FernandoB/strandberg/docs/5 way superswitch/Stewart-MacDonald_files/Steinberger_Gearless_Tuners.jpg

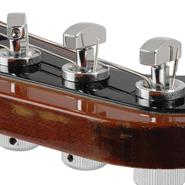
docs/5 way superswitch/Stewart-MacDonald_files/Steinberger_Gearless_Tuners.jpg
