FernandoB/strandberg/docs/#17 – Tosin Abasi _ Strandberg Guitarworks_files/IMG_47381-150x150.jpg

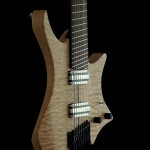
docs/#17 – Tosin Abasi _ Strandberg Guitarworks_files/IMG_47381-150x150.jpg
