FernandoB/strandberg/docs/#17 – Tosin Abasi _ Strandberg Guitarworks_files/Specs-17-150x150.jpg

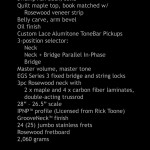
docs/#17 – Tosin Abasi _ Strandberg Guitarworks_files/Specs-17-150x150.jpg
