FernandoB/strandberg/docs/Asymmetric neck shapes – Käppi Guitars_files/Asymmetric-neck-shapes-1.png

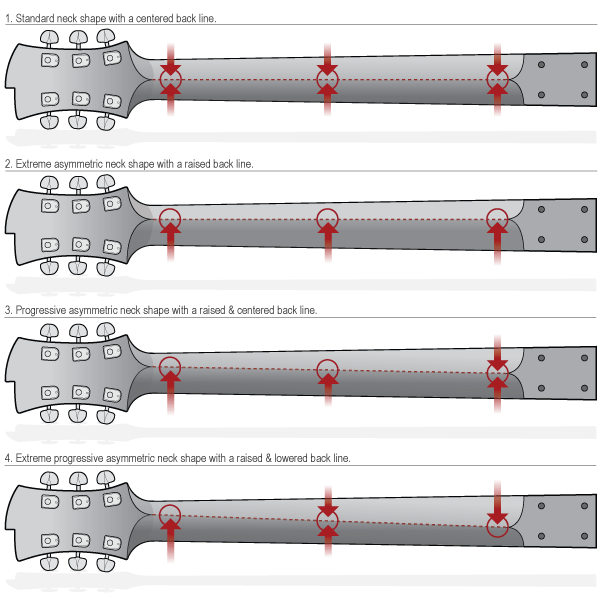
docs/Asymmetric neck shapes – Käppi Guitars_files/Asymmetric-neck-shapes-1.png
