FernandoB/strandberg/docs/boden metal white/bd7ct-17m-e-m-wp_1.png

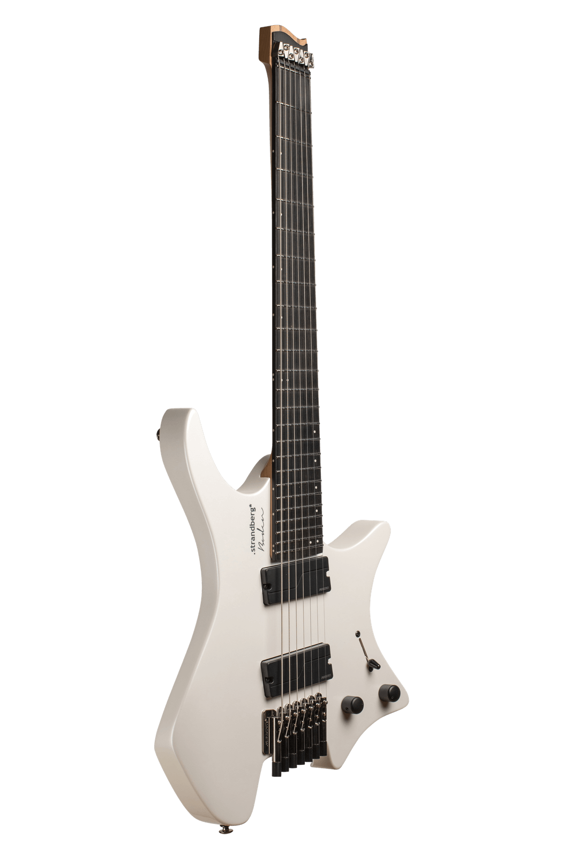
docs/boden metal white/bd7ct-17m-e-m-wp_1.png
