FernandoB/strandberg/docs/body/IMG_1061-465x620.jpg

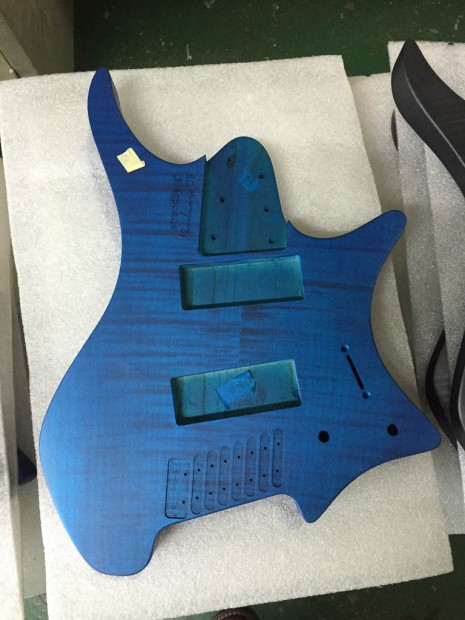
docs/body/IMG_1061-465x620.jpg
