FernandoB/strandberg/docs/body/IMG_6017.jpg

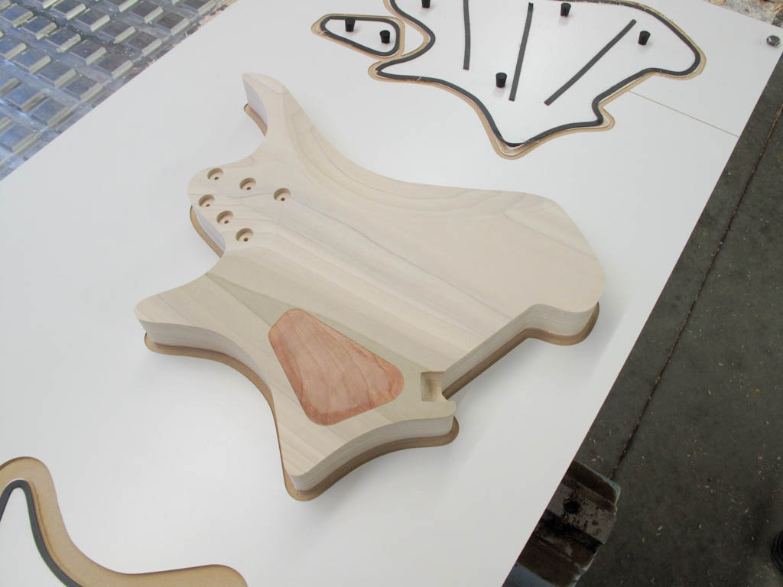
docs/body/IMG_6017.jpg
