FernandoB/strandberg/docs/body/IMG_6269.jpg

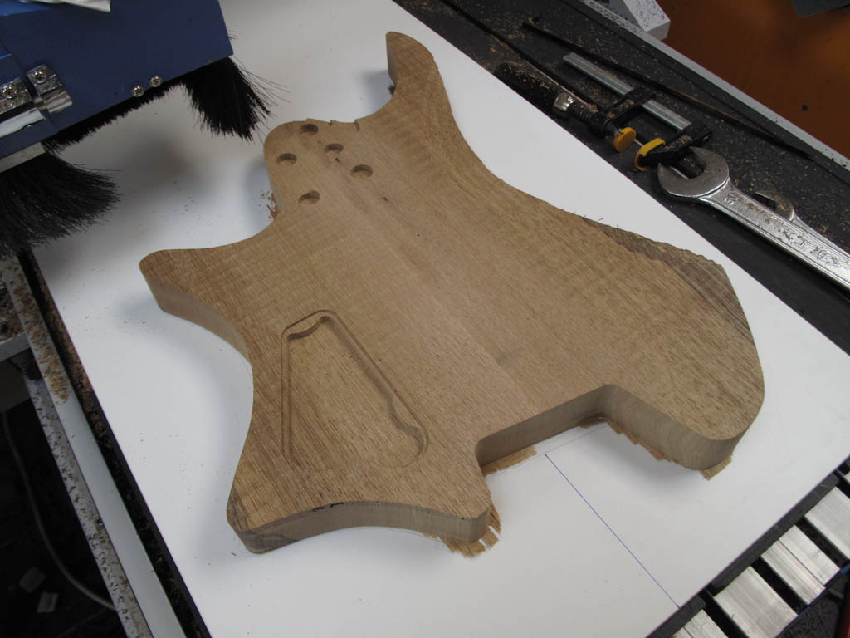
docs/body/IMG_6269.jpg
