FernandoB/strandberg/docs/fotos/5696bf7990480f4bdb856ef551d9e4b1.jpg

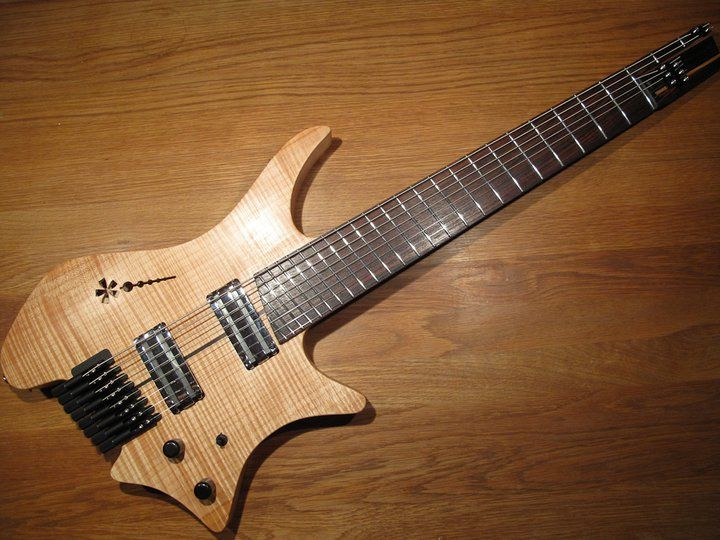
docs/fotos/5696bf7990480f4bdb856ef551d9e4b1.jpg
