FernandoB/strandberg/docs/mango/Patent Pending – The EndurNeck _ Strandberg Guitarworks_files/7s-twist.jpg

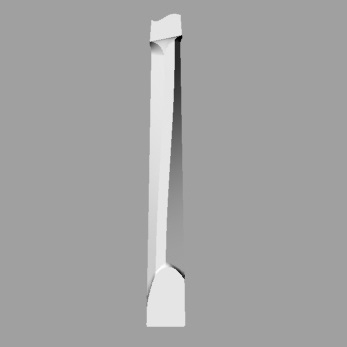
docs/mango/Patent Pending – The EndurNeck _ Strandberg Guitarworks_files/7s-twist.jpg
