FernandoB/strandberg/docs/NorthStar 8-string headless - Page 2 - In Progress and Finished Work - ProjectGuitar.com_files/IMG_1043_zpse3bc9081.jpg

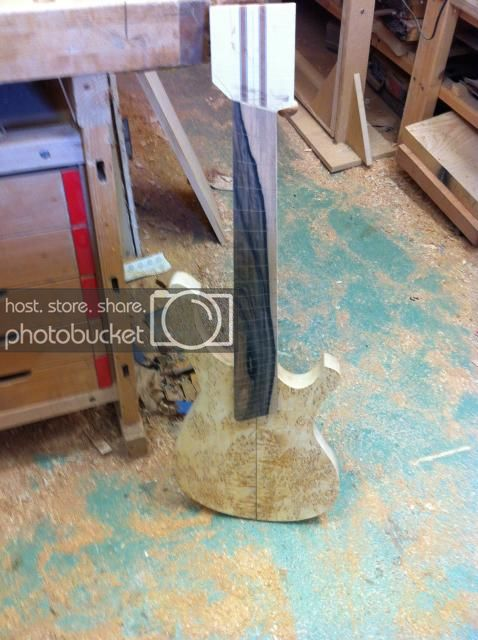
docs/NorthStar 8-string headless - Page 2 - In Progress and Finished Work - ProjectGuitar.com_files/IMG_1043_zpse3bc9081.jpg
