FernandoB/strandberg/docs/NorthStar 8-string headless - Page 2 - In Progress and Finished Work - ProjectGuitar.com_files/IMG_1084_zps51eaacd9.jpg

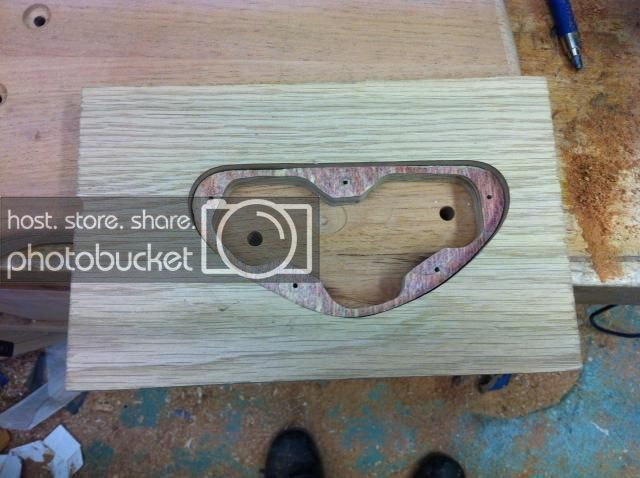
docs/NorthStar 8-string headless - Page 2 - In Progress and Finished Work - ProjectGuitar.com_files/IMG_1084_zps51eaacd9.jpg
