FernandoB/strandberg/docs/NorthStar 8-string headless - Page 2 - In Progress and Finished Work - ProjectGuitar.com_files/P4180146.jpg

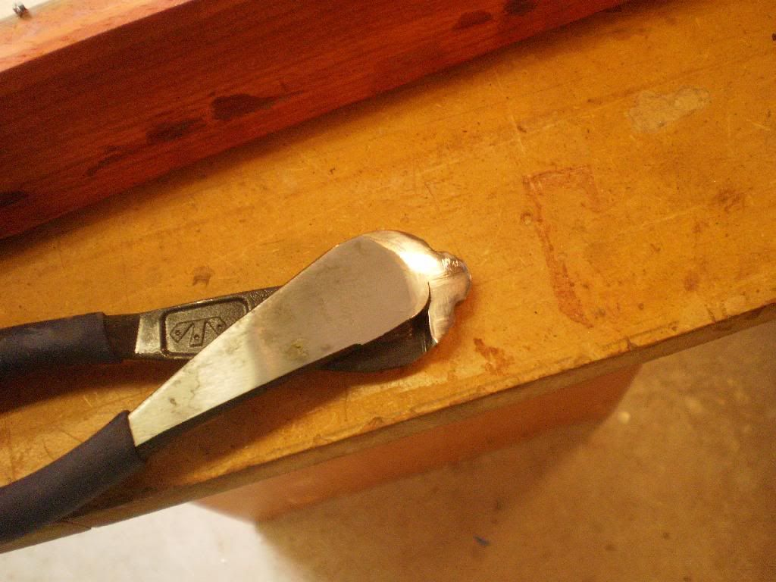
docs/NorthStar 8-string headless - Page 2 - In Progress and Finished Work - ProjectGuitar.com_files/P4180146.jpg
