FernandoB/strandberg/docs/specs/Boden Classic 7 Ghost White _ .strandberg_ Guitars_files/67343479_150905999349722_2680000513504285173_n.jpg

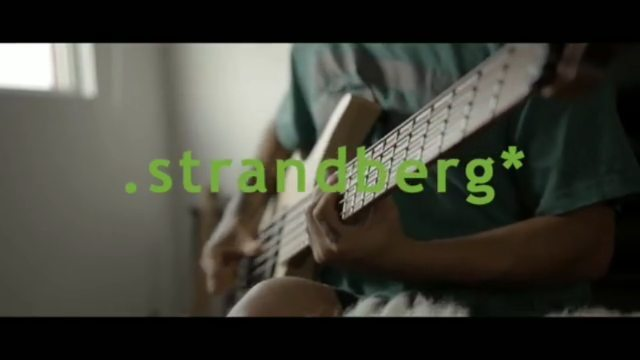
docs/specs/Boden Classic 7 Ghost White _ .strandberg_ Guitars_files/67343479_150905999349722_2680000513504285173_n.jpg
