FernandoB/strandberg/docs/specs/Boden Classic 7 Ghost White _ .strandberg_ Guitars_files/67426803_511736299582143_8697421153145143601_n.jpg

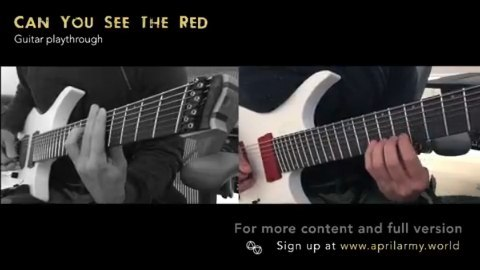
docs/specs/Boden Classic 7 Ghost White _ .strandberg_ Guitars_files/67426803_511736299582143_8697421153145143601_n.jpg
