FernandoB/strandberg/docs/specs/Boden Classic 7 Ghost White _ .strandberg_ Guitars_files/67452516_102354637756186_6294496770134847847_n.jpg

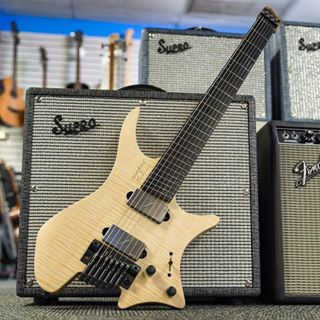
docs/specs/Boden Classic 7 Ghost White _ .strandberg_ Guitars_files/67452516_102354637756186_6294496770134847847_n.jpg
