FernandoB/strandberg/docs/specs/Boden Classic 7 Ghost White _ .strandberg_ Guitars_files/67589641_469000926987436_5073157512534394637_n.jpg

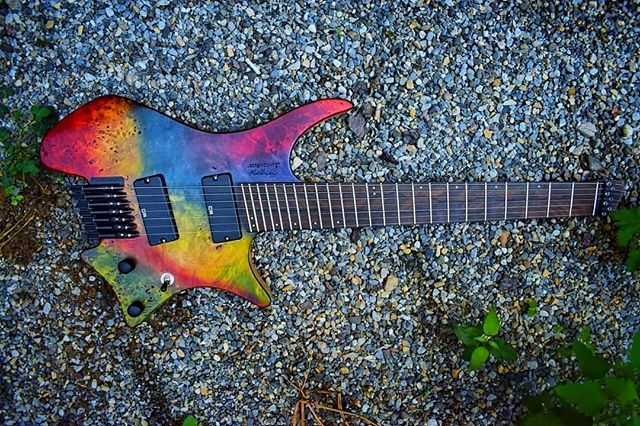
docs/specs/Boden Classic 7 Ghost White _ .strandberg_ Guitars_files/67589641_469000926987436_5073157512534394637_n.jpg
