FernandoB/strandberg/docs/specs/Boden Classic 7 Ghost White _ .strandberg_ Guitars_files/67694899_190797451917939_3582394010340054068_n.jpg

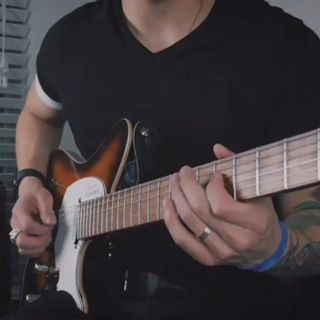
docs/specs/Boden Classic 7 Ghost White _ .strandberg_ Guitars_files/67694899_190797451917939_3582394010340054068_n.jpg
