FernandoB/strandberg/docs/specs/Boden Classic 7 Ghost White _ .strandberg_ Guitars_files/68956459_2375854755962711_6913870519651780243_n.jpg

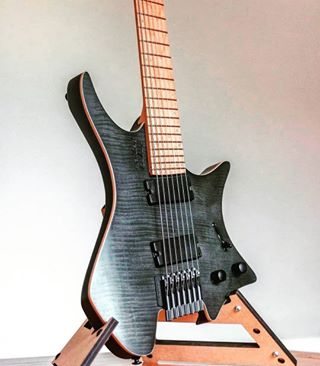
docs/specs/Boden Classic 7 Ghost White _ .strandberg_ Guitars_files/68956459_2375854755962711_6913870519651780243_n.jpg
