FernandoB/strandberg/docs/specs/Boden Classic 7 Ghost White _ .strandberg_ Guitars_files/68979052_158855945174218_2727487326449297141_n.jpg

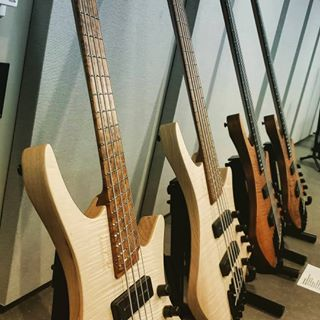
docs/specs/Boden Classic 7 Ghost White _ .strandberg_ Guitars_files/68979052_158855945174218_2727487326449297141_n.jpg
