FernandoB/strandberg/docs/specs/Boden Classic 7 Ghost White _ .strandberg_ Guitars_files/69485622_2290564877940070_366146129192254861_n.jpg

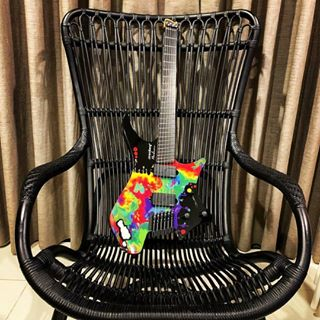
docs/specs/Boden Classic 7 Ghost White _ .strandberg_ Guitars_files/69485622_2290564877940070_366146129192254861_n.jpg
