FernandoB/strandberg/docs/specs/Boden Classic 7 Ghost White _ .strandberg_ Guitars_files/69579608_494088754658758_1485637827757459320_n.jpg

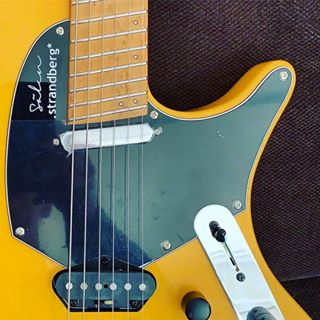
docs/specs/Boden Classic 7 Ghost White _ .strandberg_ Guitars_files/69579608_494088754658758_1485637827757459320_n.jpg
