FernandoB/strandberg/docs/specs/Boden Classic 7 Ghost White _ .strandberg_ Guitars_files/69621913_944535012569313_5548777814130400954_n.jpg

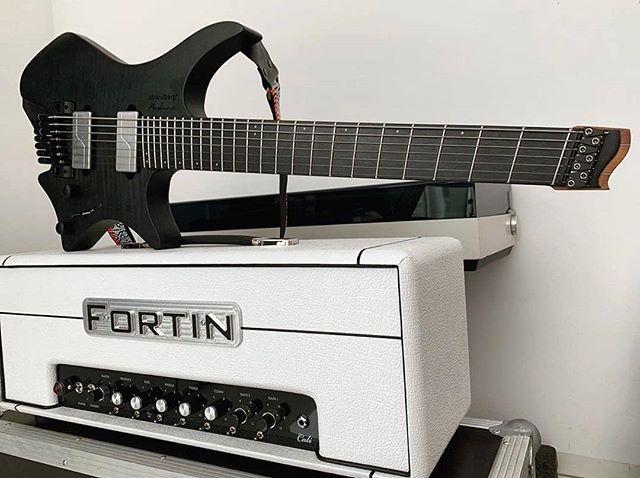
docs/specs/Boden Classic 7 Ghost White _ .strandberg_ Guitars_files/69621913_944535012569313_5548777814130400954_n.jpg
