FernandoB/strandberg/docs/specs/Boden Classic 7 Ghost White _ .strandberg_ Guitars_files/bd7ct-17o-m-f-bk_a-606x909.webp

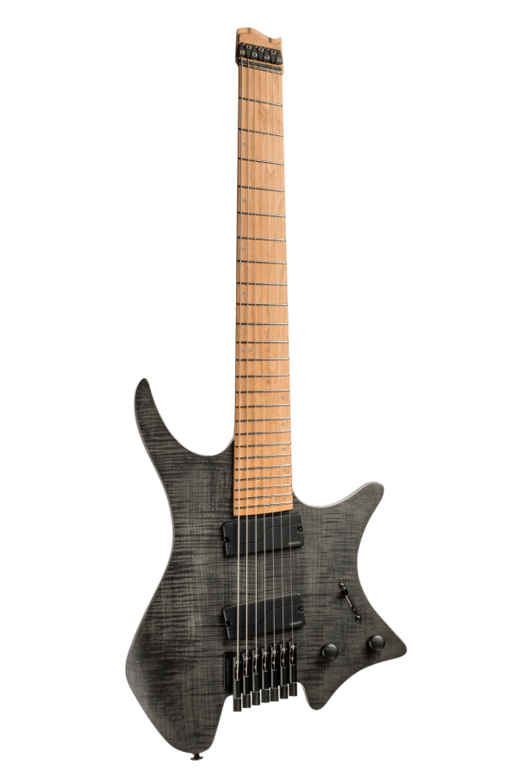
docs/specs/Boden Classic 7 Ghost White _ .strandberg_ Guitars_files/bd7ct-17o-m-f-bk_a-606x909.webp
