FernandoB/strandberg/docs/specs/Boden Classic 7 Ghost White _ .strandberg_ Guitars_files/bd7ct-18c-m-a-gw_4-160x240.png

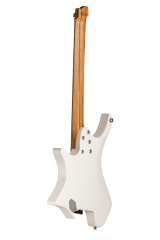
docs/specs/Boden Classic 7 Ghost White _ .strandberg_ Guitars_files/bd7ct-18c-m-a-gw_4-160x240.png
