FernandoB/strandberg/docs/specs/Boden Classic 7 Ghost White _ .strandberg_ Guitars_files/bkg-boden-classic.webp

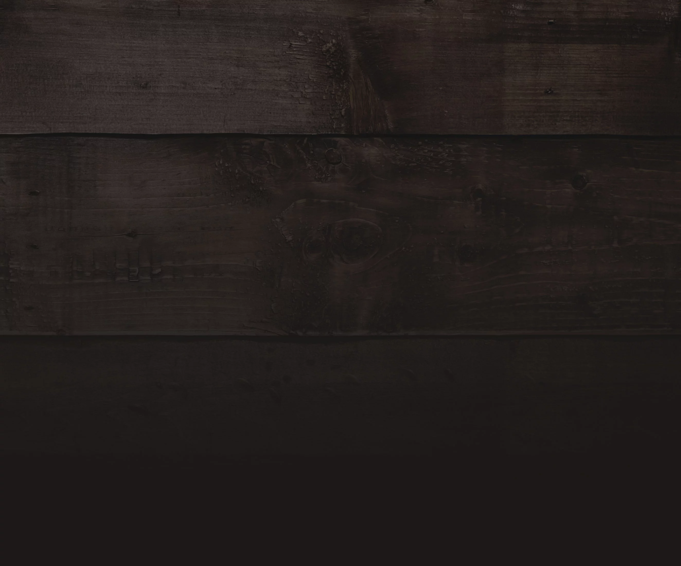
docs/specs/Boden Classic 7 Ghost White _ .strandberg_ Guitars_files/bkg-boden-classic.webp
