FernandoB/strandberg/docs/specs/Boden Classic 7 Ghost White _ .strandberg_ Guitars_files/boden_classic_beauty_shot_1.webp

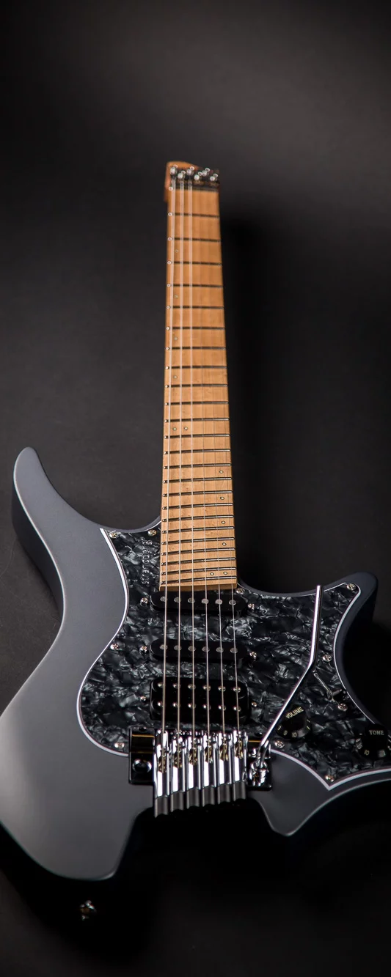
docs/specs/Boden Classic 7 Ghost White _ .strandberg_ Guitars_files/boden_classic_beauty_shot_1.webp
