FernandoB/strandberg/docs/specs/Boden Classic 7 Ghost White _ .strandberg_ Guitars_files/boden_machacek_beauty_shot_7-720x664.webp

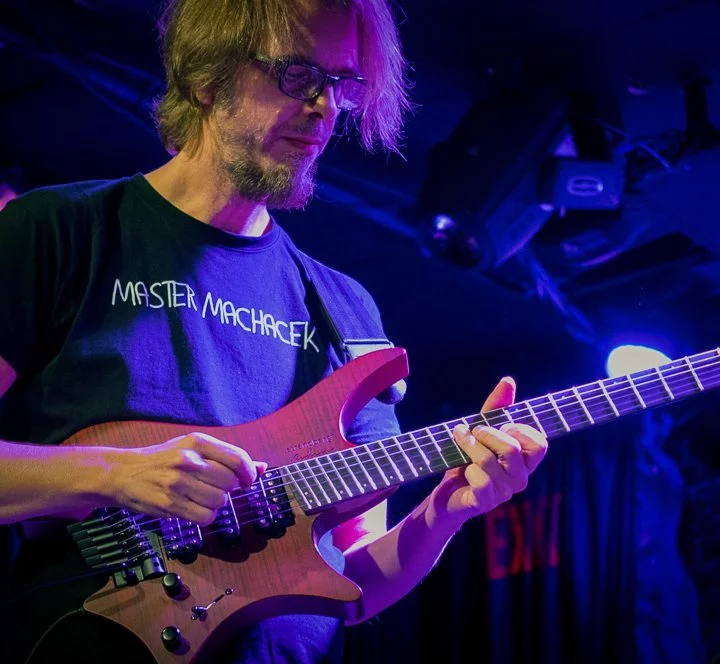
docs/specs/Boden Classic 7 Ghost White _ .strandberg_ Guitars_files/boden_machacek_beauty_shot_7-720x664.webp
