FernandoB/strandberg/docs/specs/Boden Classic 7 Ghost White _ .strandberg_ Guitars_files/headless_design_bullet_round-150x150.webp

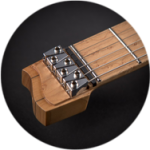
docs/specs/Boden Classic 7 Ghost White _ .strandberg_ Guitars_files/headless_design_bullet_round-150x150.webp
