FernandoB/strandberg/docs/specs/Boden Classic 7 Ghost White _ .strandberg_ Guitars_files/img_8952-e1481700775124-720x720.webp

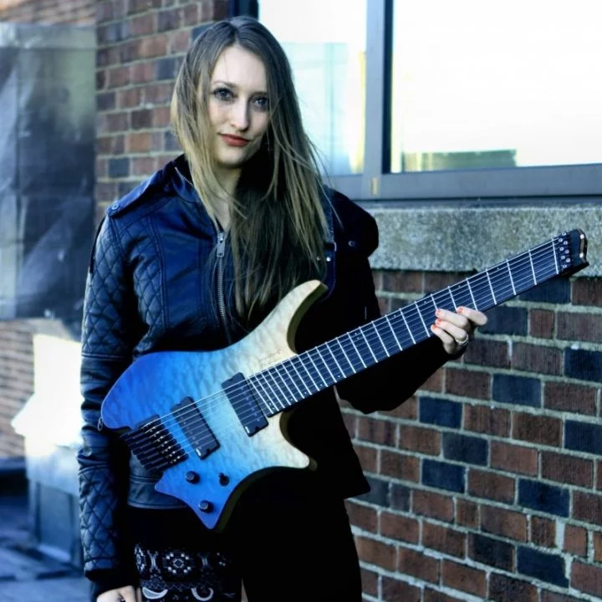
docs/specs/Boden Classic 7 Ghost White _ .strandberg_ Guitars_files/img_8952-e1481700775124-720x720.webp
