FernandoB/strandberg/docs/specs/Boden Classic 7 Ghost White _ .strandberg_ Guitars_files/mike_keneally_landscape-720x720.webp

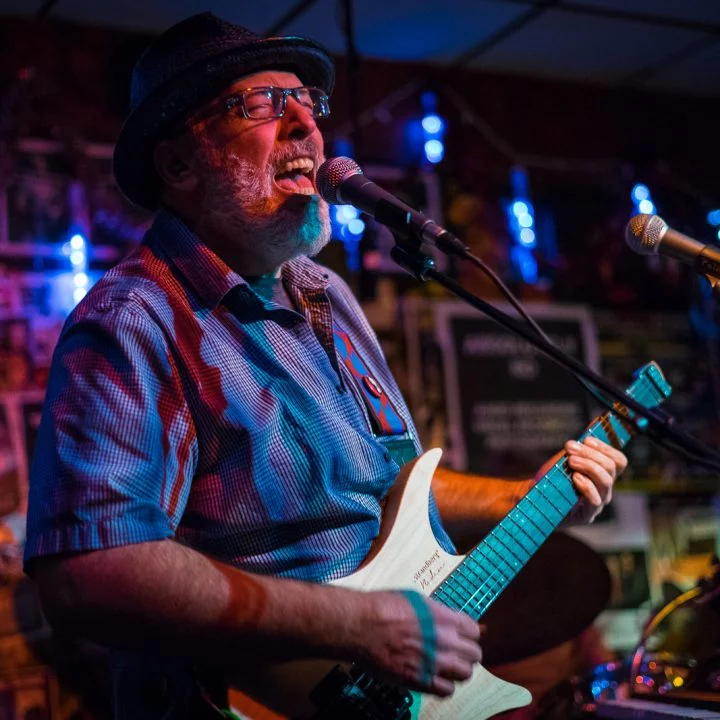
docs/specs/Boden Classic 7 Ghost White _ .strandberg_ Guitars_files/mike_keneally_landscape-720x720.webp
