FernandoB/strandberg/docs/specs/Boden Metal 7 White Pearl _ .strandberg_ Guitars_files/bd7ct-17m-e-m-wp_c-160x240.webp

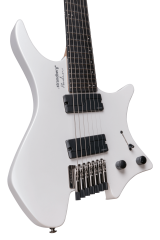
docs/specs/Boden Metal 7 White Pearl _ .strandberg_ Guitars_files/bd7ct-17m-e-m-wp_c-160x240.webp
