FernandoB/strandberg/docs/specs/Boden Metal 7 White Pearl _ .strandberg_ Guitars_files/bkg-metal.webp

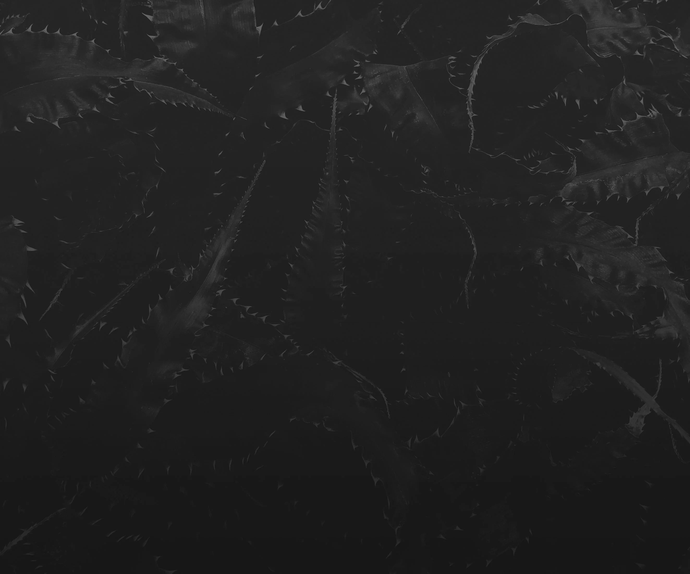
docs/specs/Boden Metal 7 White Pearl _ .strandberg_ Guitars_files/bkg-metal.webp
