FernandoB/strandberg/docs/specs/Boden Metal 7 White Pearl _ .strandberg_ Guitars_files/boden_metal_beauty_shot_2.webp

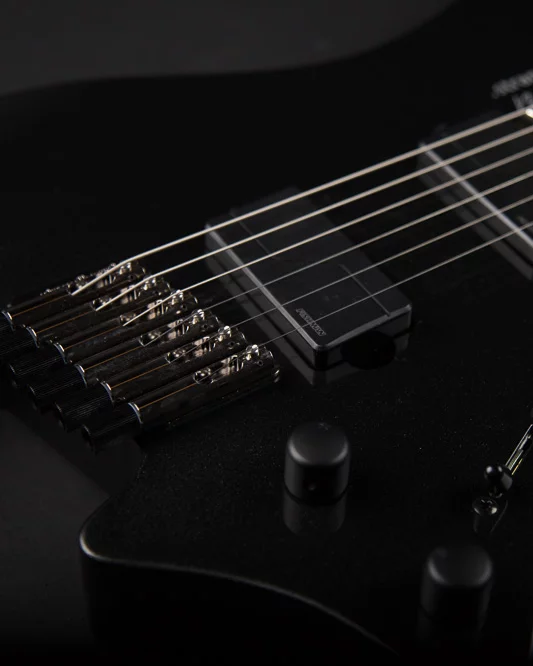
docs/specs/Boden Metal 7 White Pearl _ .strandberg_ Guitars_files/boden_metal_beauty_shot_2.webp
