FernandoB/strandberg/docs/specs/Boden Standard 7 Maple Flame Blue _ .strandberg_ Guitars_files/bd7ct-18s-m-fv-bl_1-160x240.webp

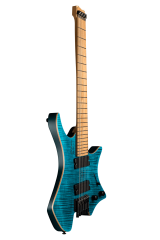
docs/specs/Boden Standard 7 Maple Flame Blue _ .strandberg_ Guitars_files/bd7ct-18s-m-fv-bl_1-160x240.webp
