FernandoB/strandberg/docs/specs/Boden Standard 7 Maple Flame Blue _ .strandberg_ Guitars_files/bd7tct-17o-m-f-rd_a-606x909.webp

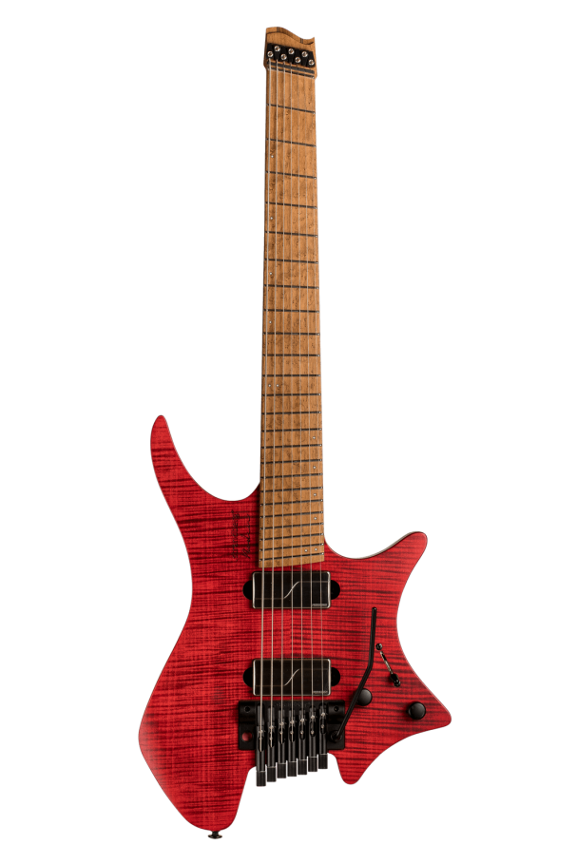
docs/specs/Boden Standard 7 Maple Flame Blue _ .strandberg_ Guitars_files/bd7tct-17o-m-f-rd_a-606x909.webp
