FernandoB/strandberg/docs/specs/Boden Standard 7 Maple Flame Blue _ .strandberg_ Guitars_files/bkg-standard.jpg

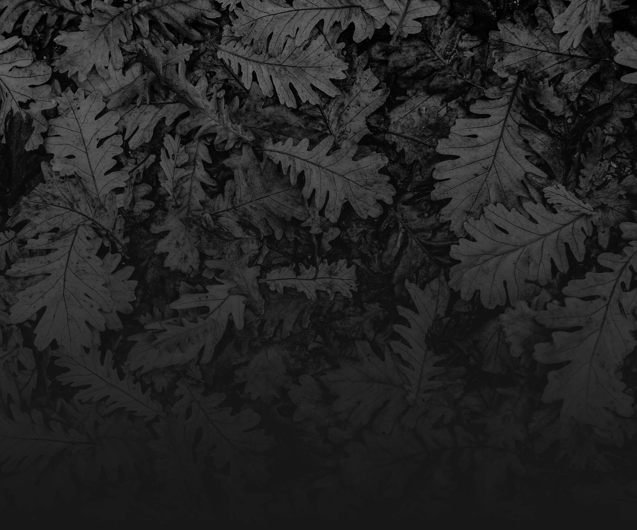
docs/specs/Boden Standard 7 Maple Flame Blue _ .strandberg_ Guitars_files/bkg-standard.jpg
