FernandoB/strandberg/docs/specs/Boden Standard 7 Maple Flame Blue _ .strandberg_ Guitars_files/boden_standard_beauty_shot_1.webp

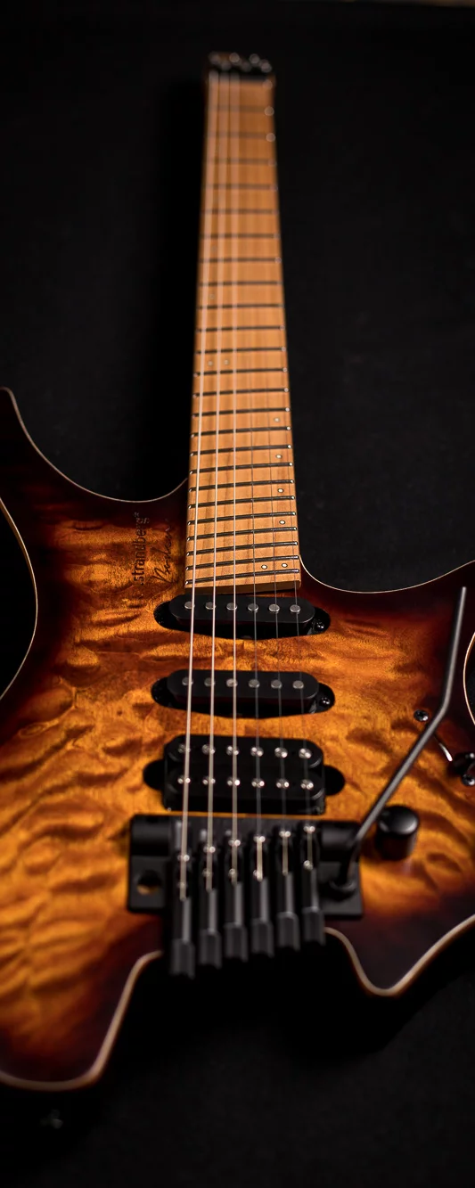
docs/specs/Boden Standard 7 Maple Flame Blue _ .strandberg_ Guitars_files/boden_standard_beauty_shot_1.webp
