FernandoB/strandberg/docs/wiring/#61 Wiring _ Strandberg Guitarworks_files/61-Schematic-300x217.png

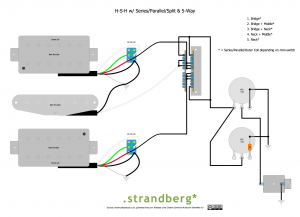
docs/wiring/#61 Wiring _ Strandberg Guitarworks_files/61-Schematic-300x217.png
