FernandoB/strandberg/docs/wiring/#65 Wiring _ Strandberg Guitarworks_files/65-Schematic-300x217.png

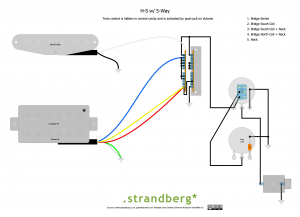
docs/wiring/#65 Wiring _ Strandberg Guitarworks_files/65-Schematic-300x217.png
