FernandoB/strandberg/photos/20210119_215234.jpg

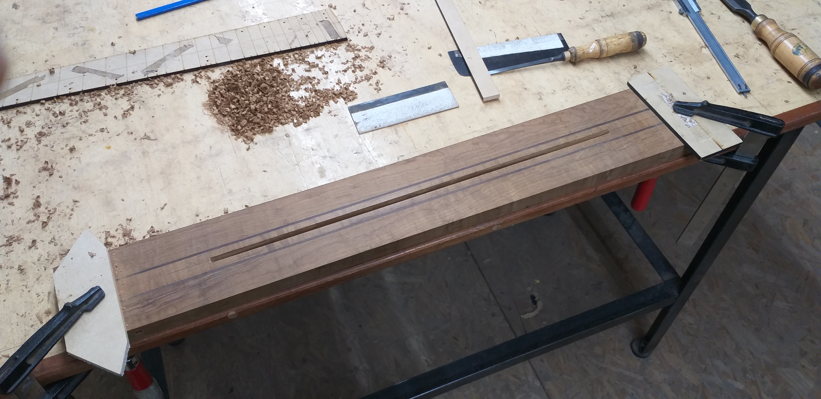
photos/20210119_215234.jpg
