FernandoB/strandberg/photos/20210209_213849.jpg

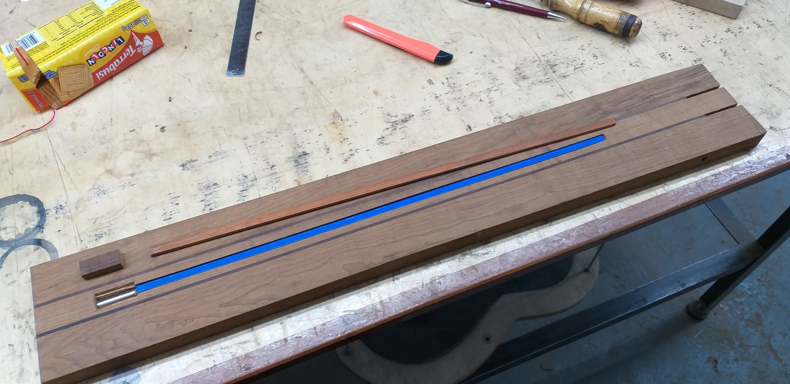
photos/20210209_213849.jpg
