FernandoB/strandberg/photos/20210223_215921.jpg

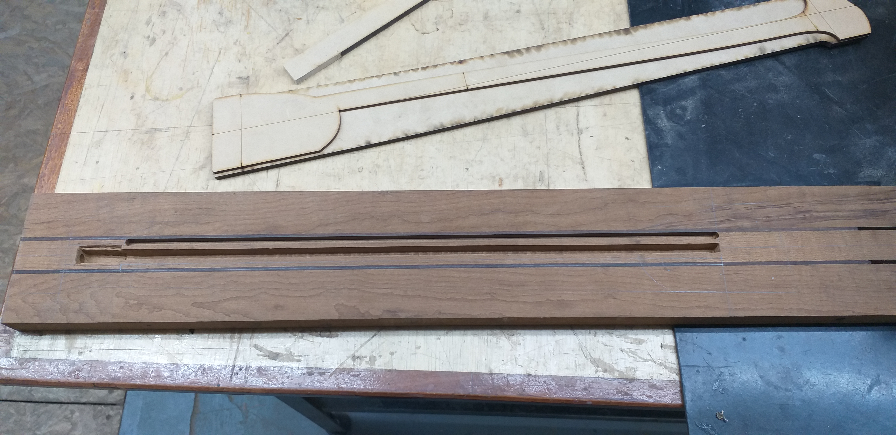
photos/20210223_215921.jpg
