FernandoB/strandberg/photos/20210330_215819.jpg

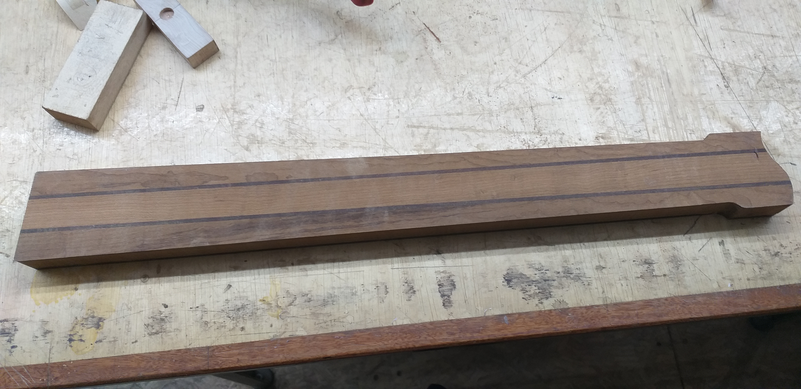
photos/20210330_215819.jpg
