FernandoB/strandberg/photos/20210406_194518.jpg

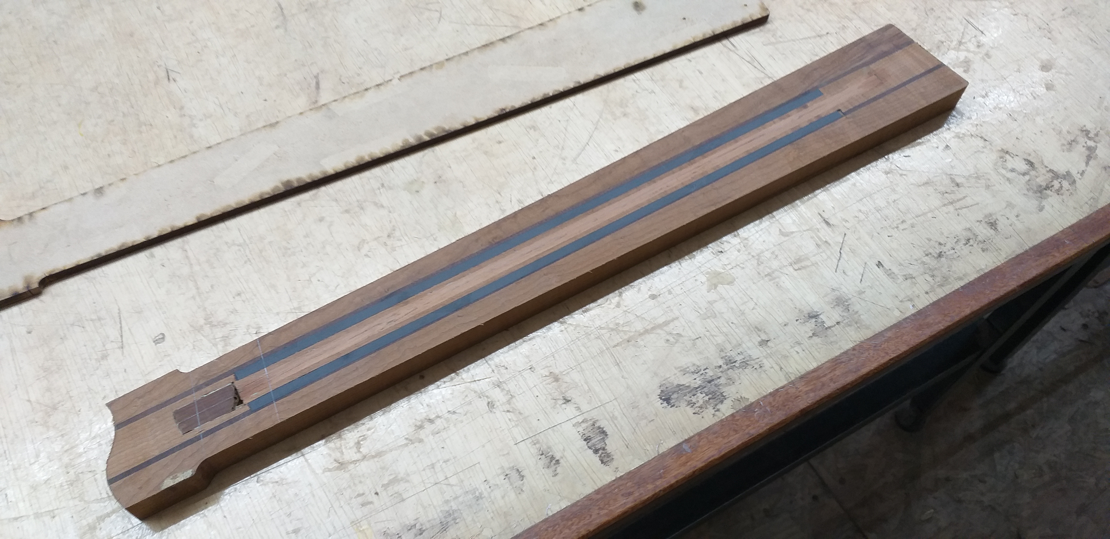
photos/20210406_194518.jpg
