FernandoB/strandberg/photos/20210427_192807.jpg

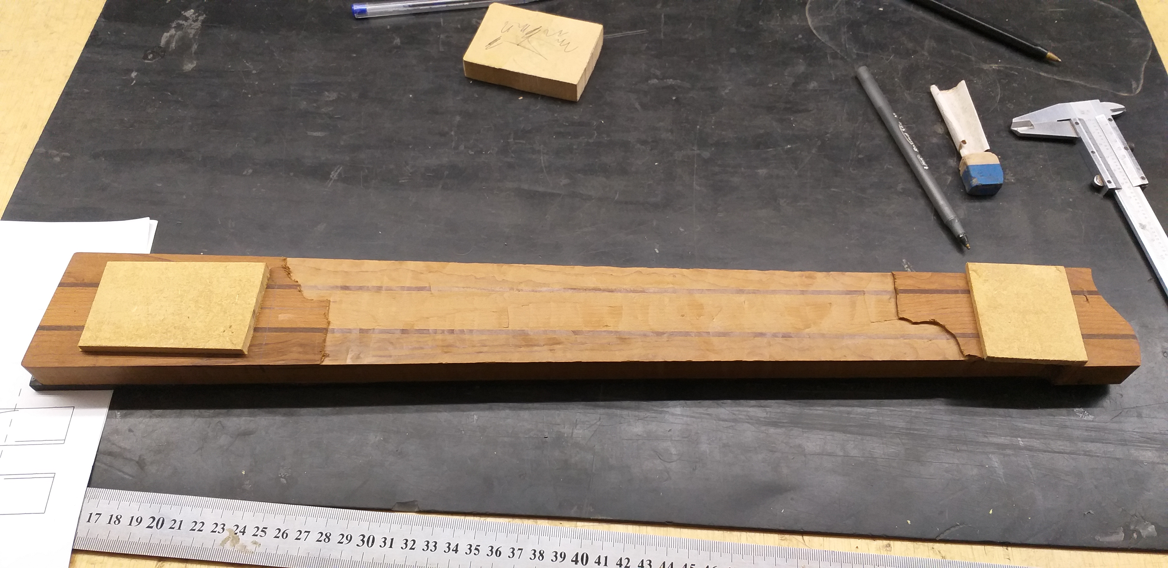
photos/20210427_192807.jpg
