FernandoB/strandberg/photos/20210713_215407.jpg

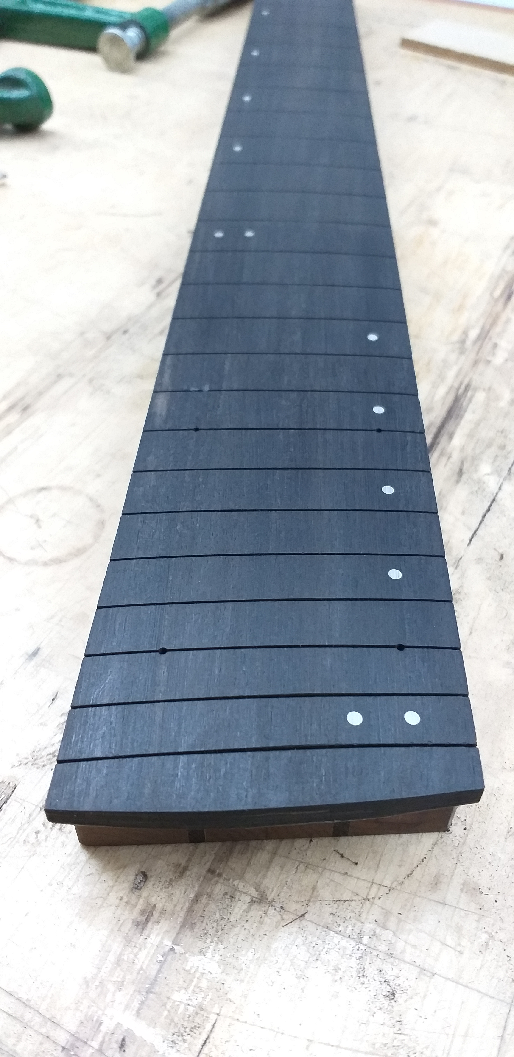
photos/20210713_215407.jpg
