FernandoB/strandberg/photos/20211012_215354.jpg

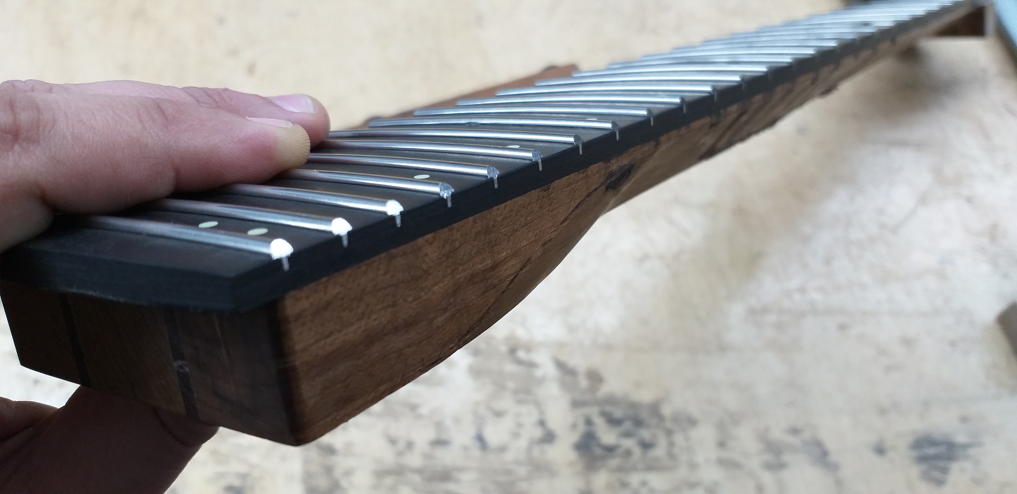
photos/20211012_215354.jpg
