FernandoB/strandberg/photos/20220315_215535.jpg

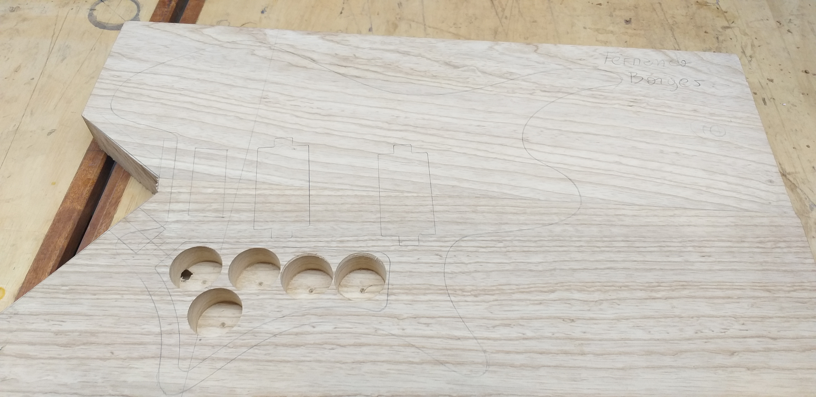
photos/20220315_215535.jpg
