FernandoB/strandberg/photos/20220329_215044.jpg

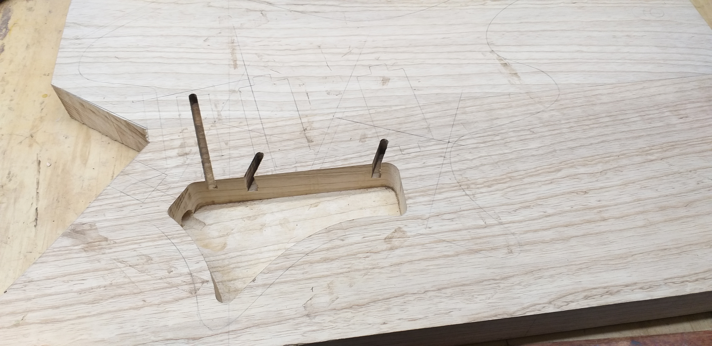
photos/20220329_215044.jpg
