FernandoB/strandberg/photos/20220419_215206.jpg

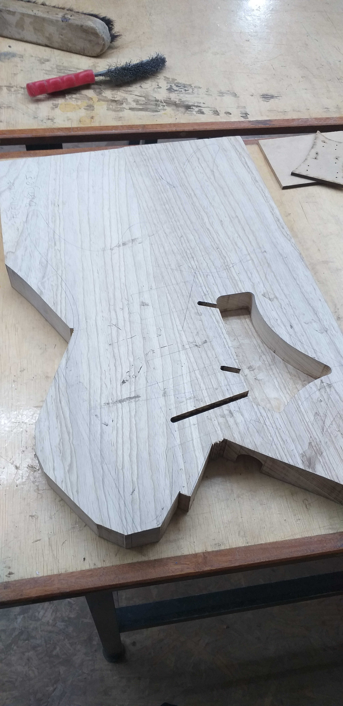
photos/20220419_215206.jpg
