FernandoB/strandberg/photos/20220614_215217.jpg

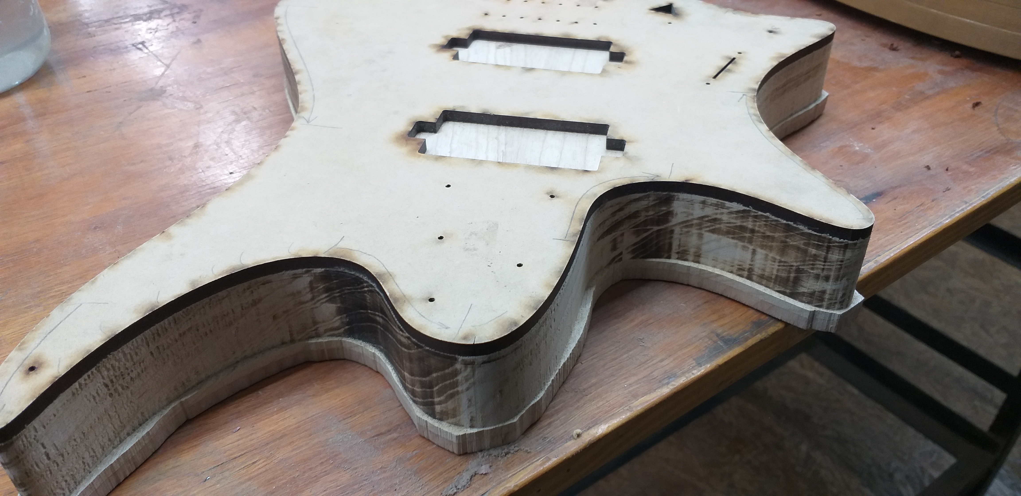
photos/20220614_215217.jpg
