FernandoB/strandberg/photos/20221004_215103.jpg

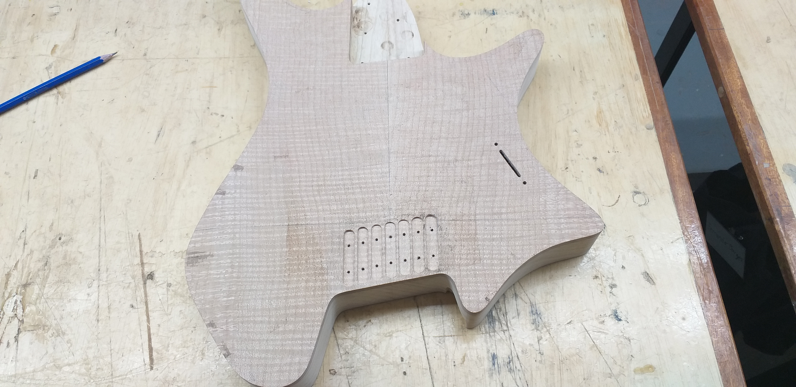
photos/20221004_215103.jpg
