FernandoB/strandberg/photos/20221018_213631.jpg

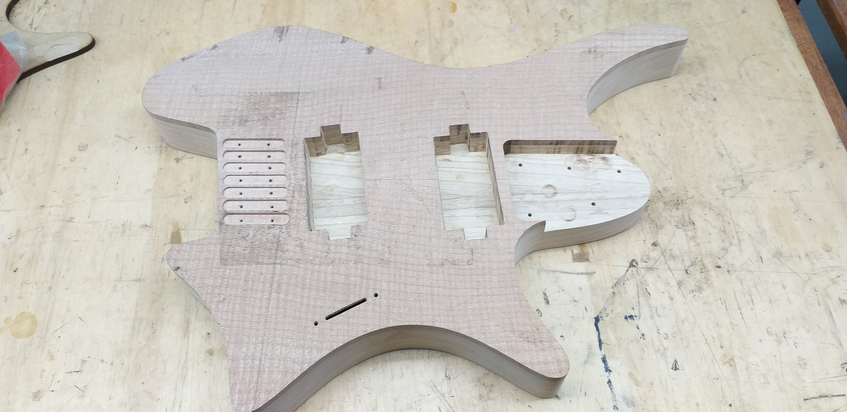
photos/20221018_213631.jpg
