FernandoB/strandberg/photos/20221018_215050.jpg

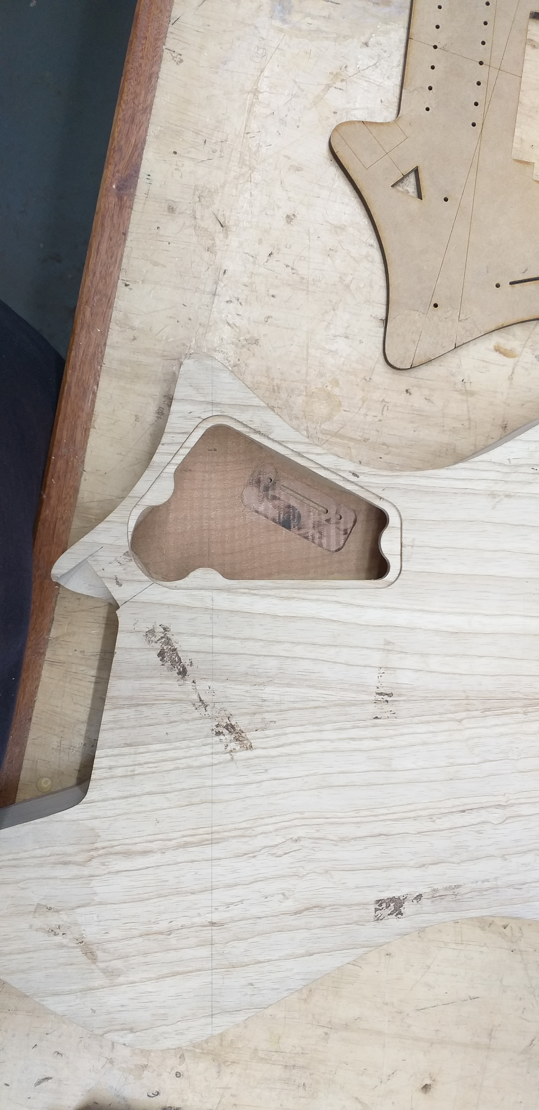
photos/20221018_215050.jpg
