FernandoB/strandberg/photos/20221018_215109.jpg

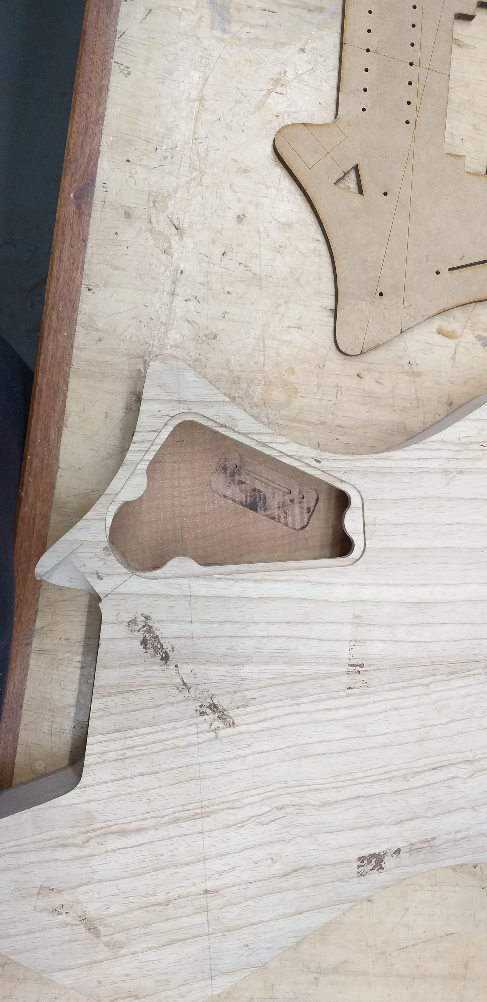
photos/20221018_215109.jpg
