FernandoB/strandberg/photos/20221108_215148.jpg

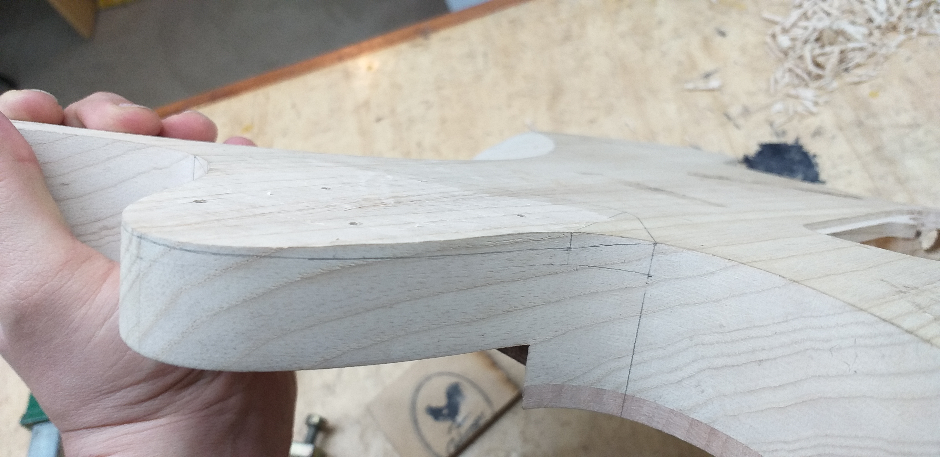
photos/20221108_215148.jpg
