FernandoB/strandberg/photos/20221115_215245.jpg

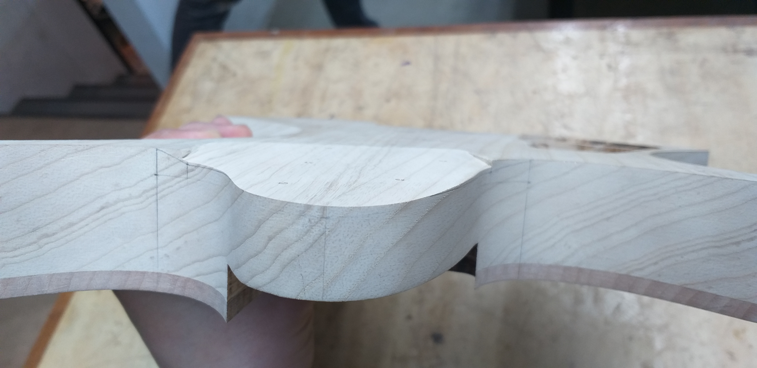
photos/20221115_215245.jpg
