FernandoB/strandberg/photos/20221122_213335.jpg

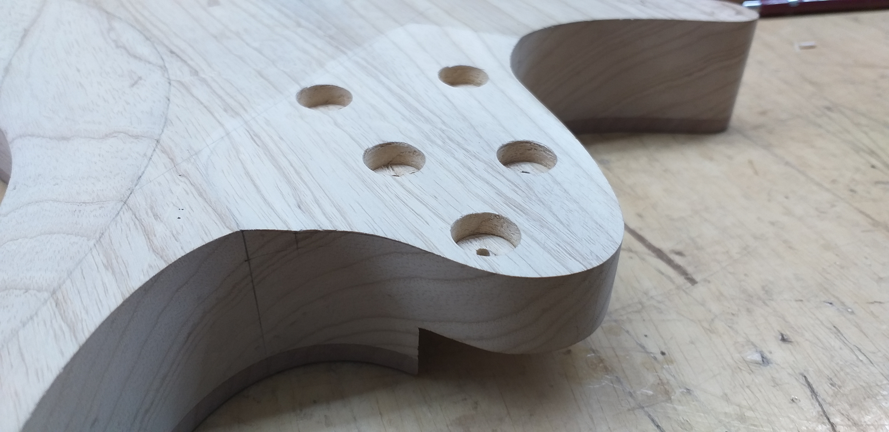
photos/20221122_213335.jpg
