FernandoB/strandberg/photos/20221222_201924.jpg

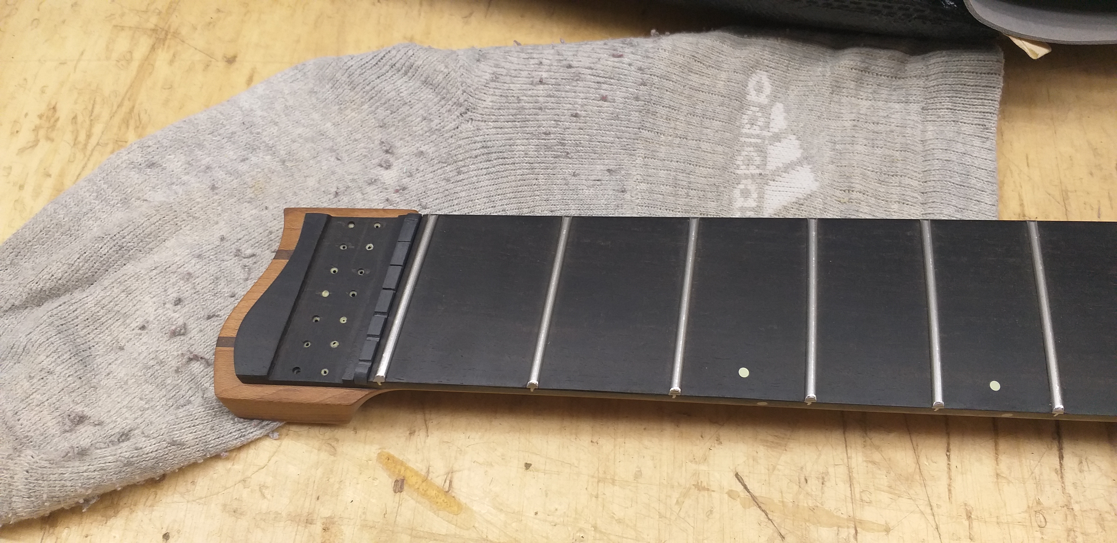
photos/20221222_201924.jpg
