FernandoB/strandberg/photos/20230228_214408.jpg

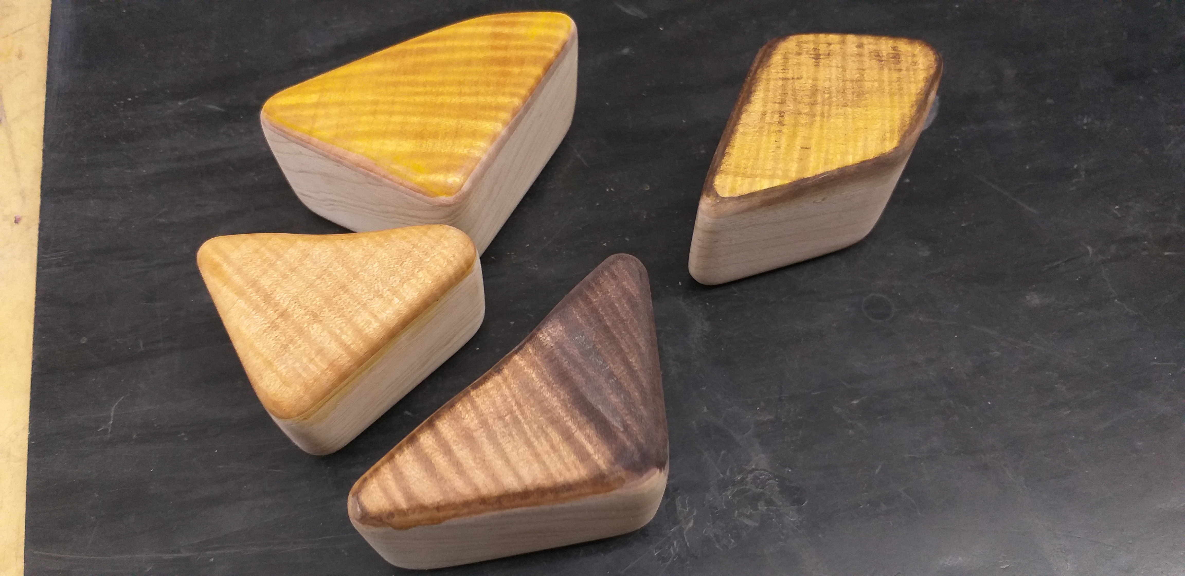
photos/20230228_214408.jpg
