FernandoB/strandberg/photos/20230411_212509.jpg

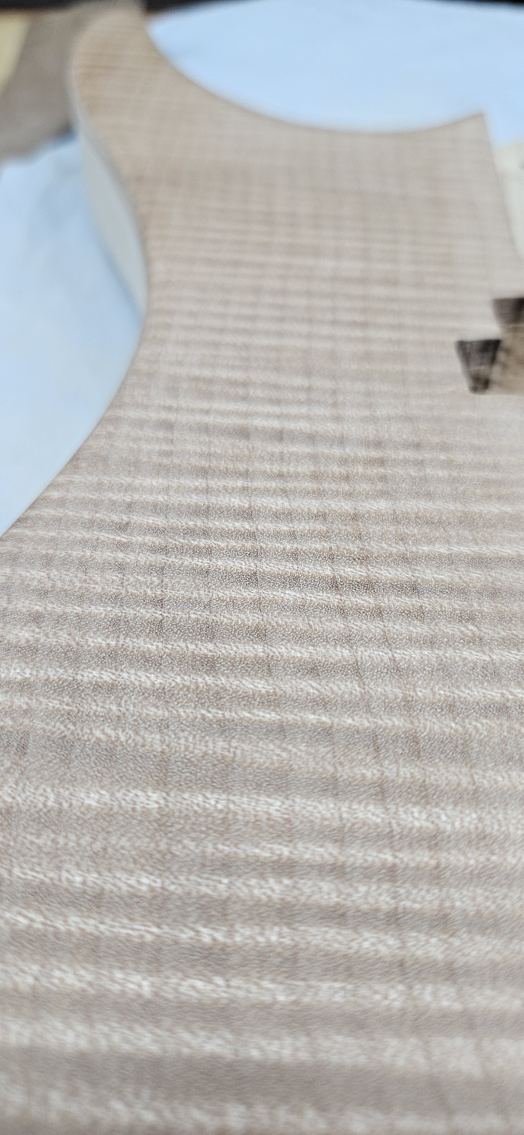
photos/20230411_212509.jpg
