FernandoB/strandberg/photos/20230411_212559.jpg

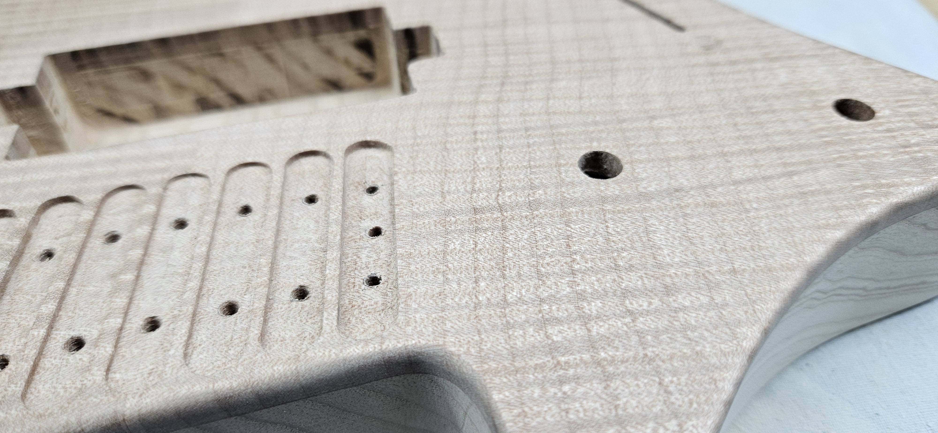
photos/20230411_212559.jpg
