FernandoB/strandberg/photos/20230530_205302.jpg

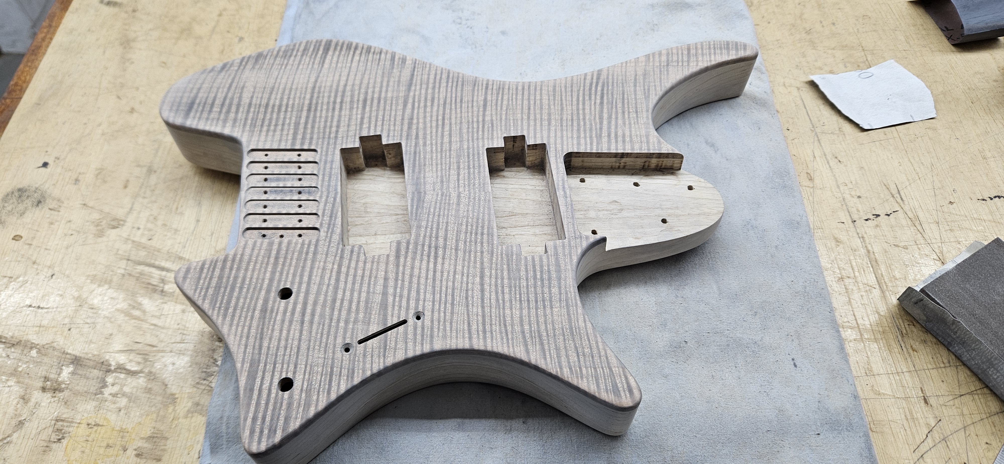
photos/20230530_205302.jpg
