FernandoB/strandberg/photos/20230530_215438.jpg

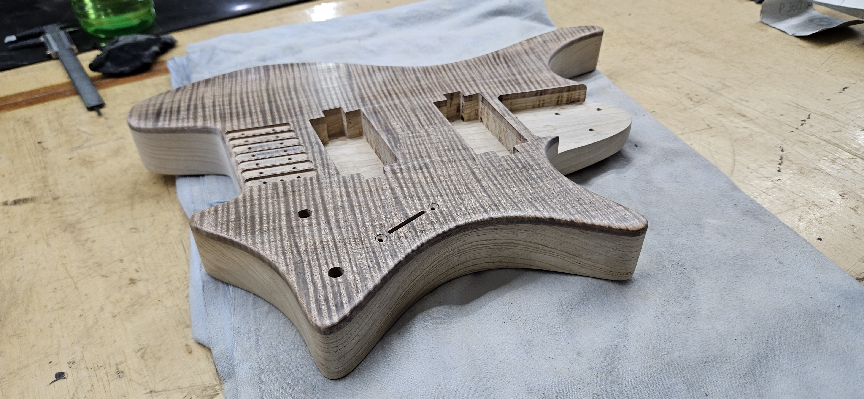
photos/20230530_215438.jpg
