FernandoB/strandberg/photos/20230711_215309.jpg

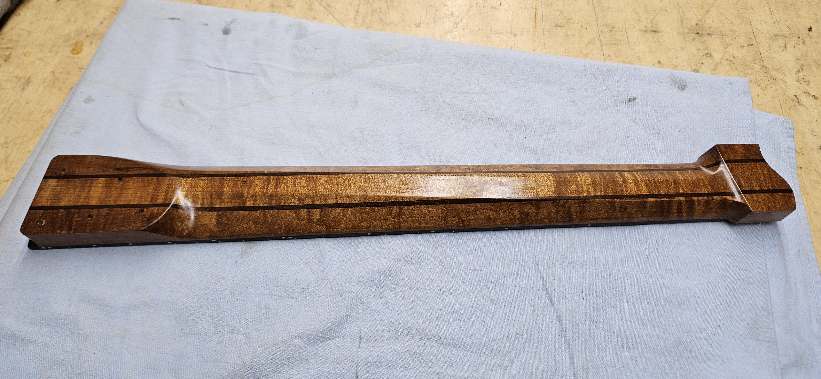
photos/20230711_215309.jpg
