FernandoB/strandberg/photos/20230808_203318.jpg

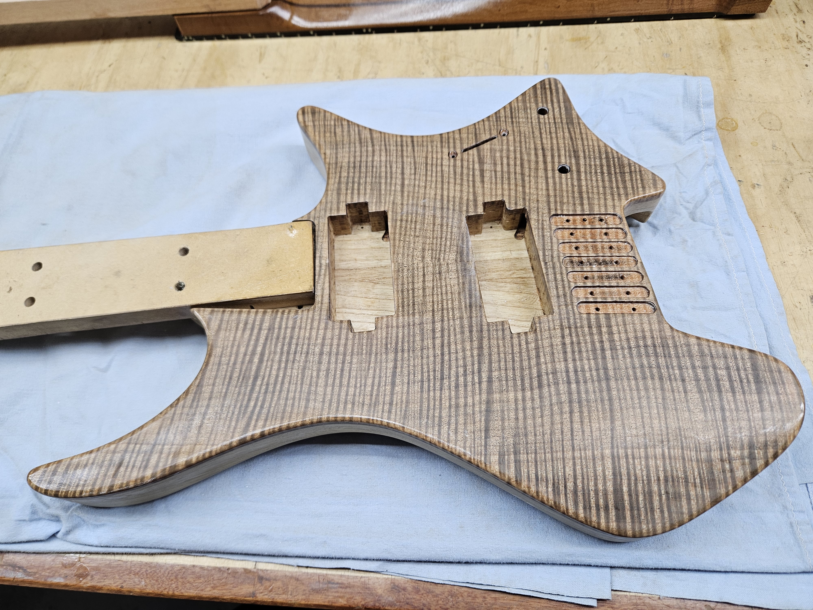
photos/20230808_203318.jpg
