FernandoB/strandberg/photos/20231010_213619.jpg

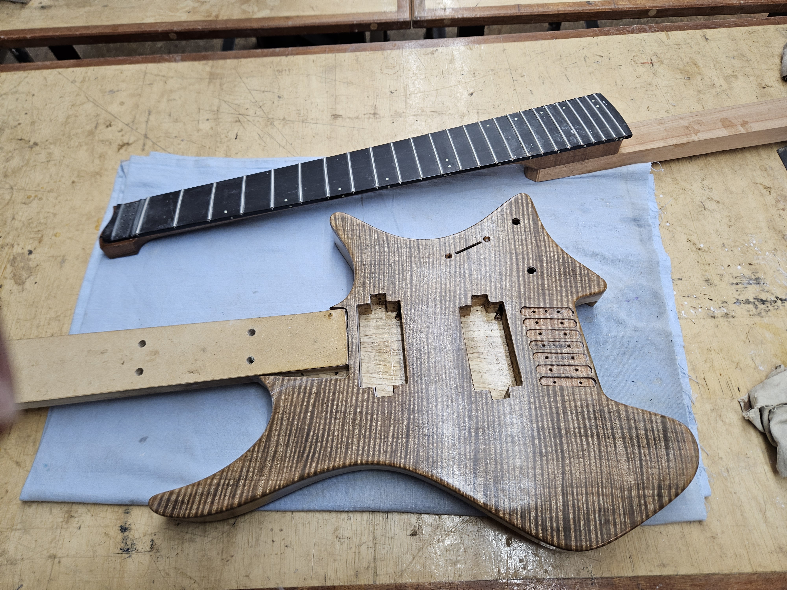
photos/20231010_213619.jpg
