FernandoB/strandberg/photos/20240723_220008.jpg

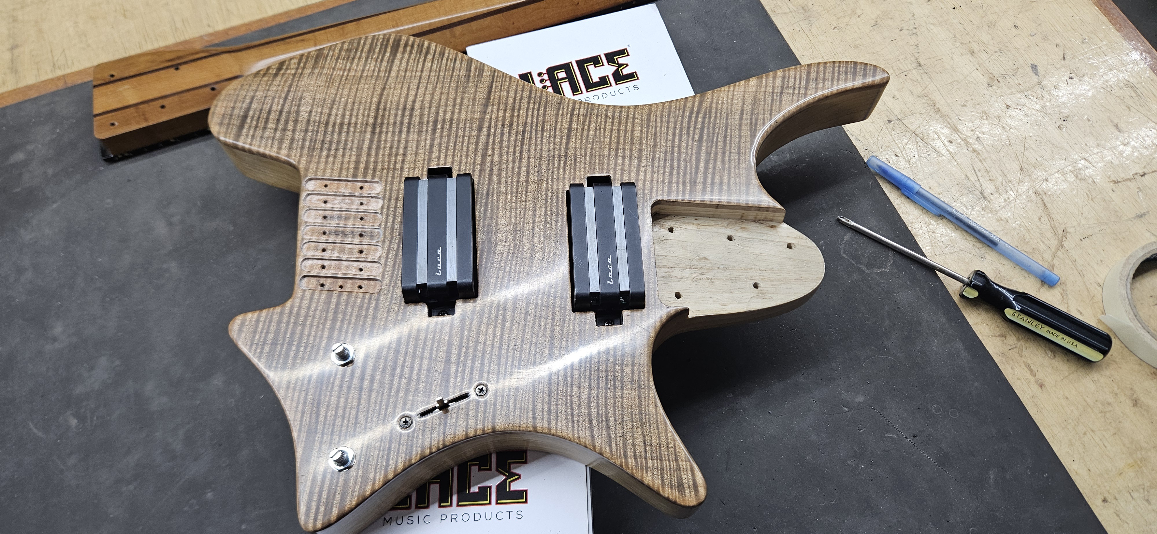
photos/20240723_220008.jpg
