FernandoB/strandberg/photos/20240730_210756.jpg

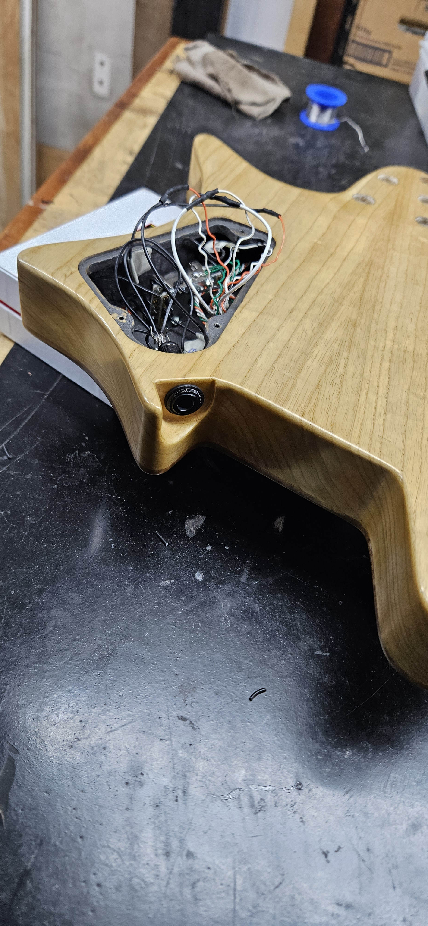
photos/20240730_210756.jpg
