FernandoB/strandberg/photos/20240730_215359.jpg

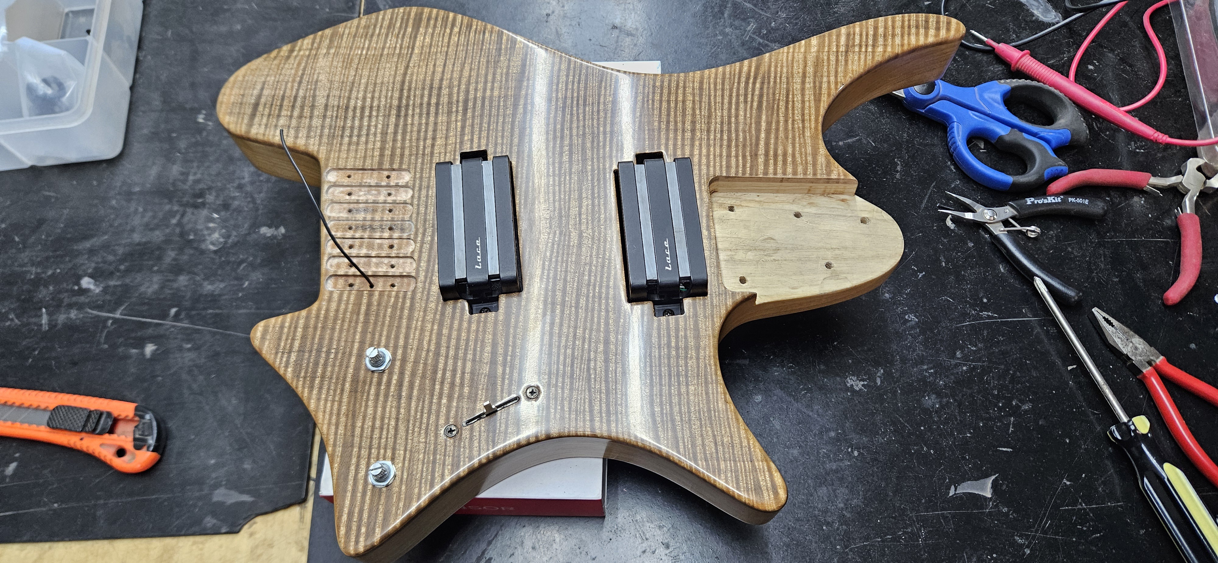
photos/20240730_215359.jpg
