FernandoB/strandberg/photos/20240813_194406.jpg

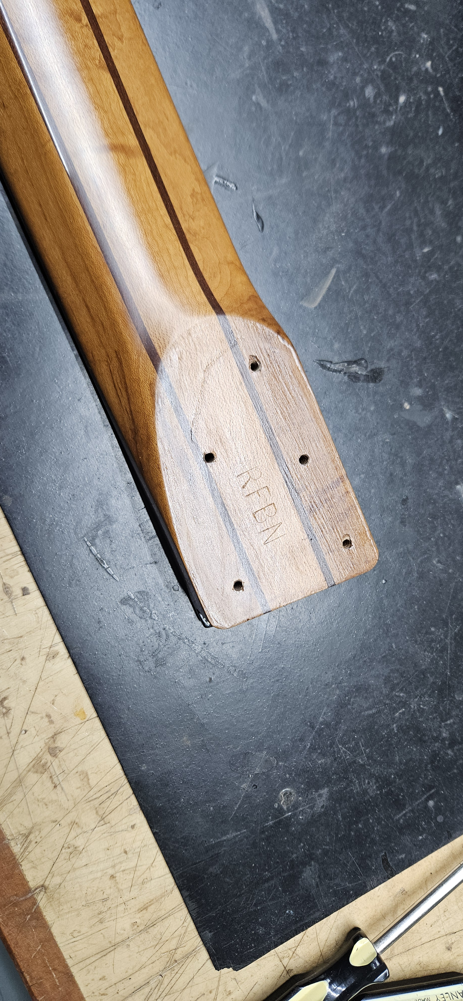
photos/20240813_194406.jpg
