FernandoB/strandberg/photos/20240910_221057.jpg

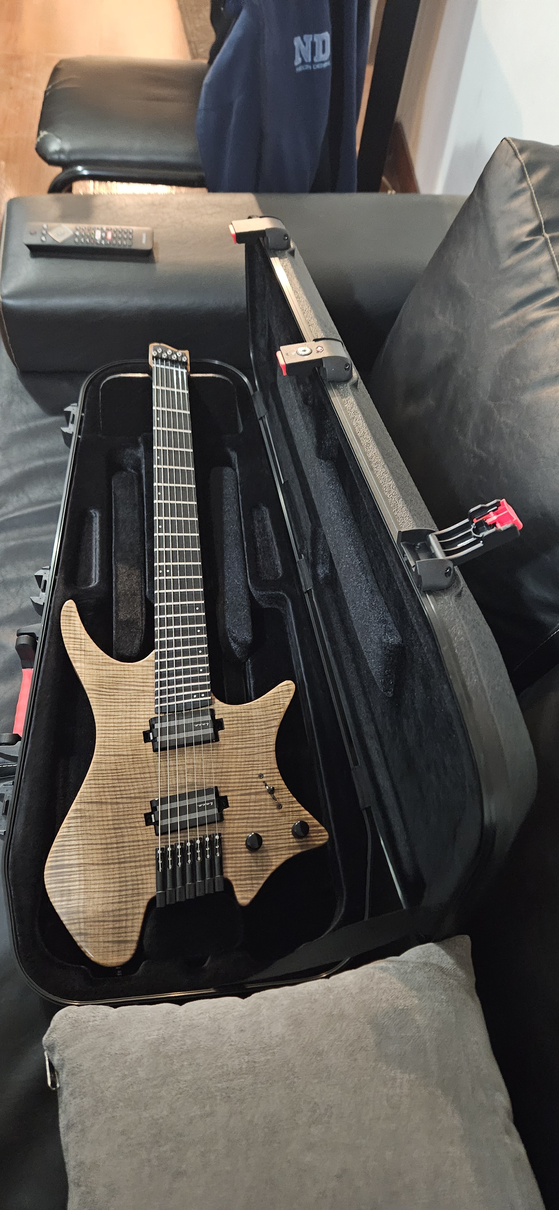
photos/20240910_221057.jpg
