FernandoB/strandberg/photos/IMG-20240910-WA0012.jpg

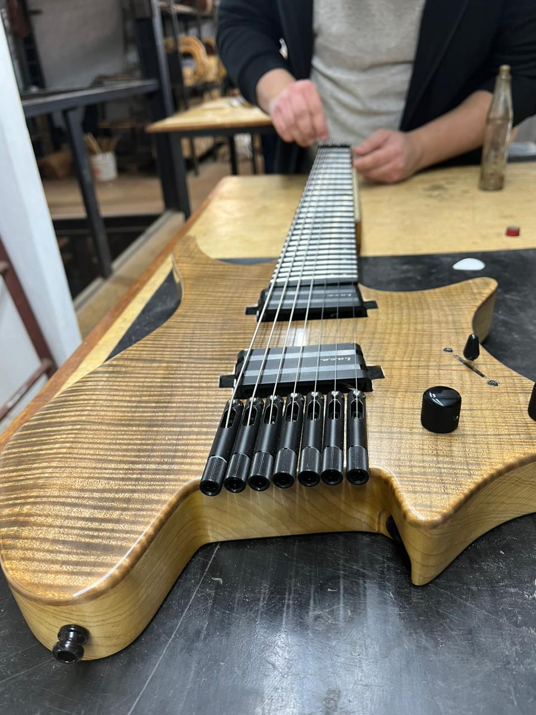
photos/IMG-20240910-WA0012.jpg
