FernandoB/strandberg/docs/3D Printed Nuts _ Strandberg Guitarworks_files/FullSizeRender-5-1024x1024.jpg

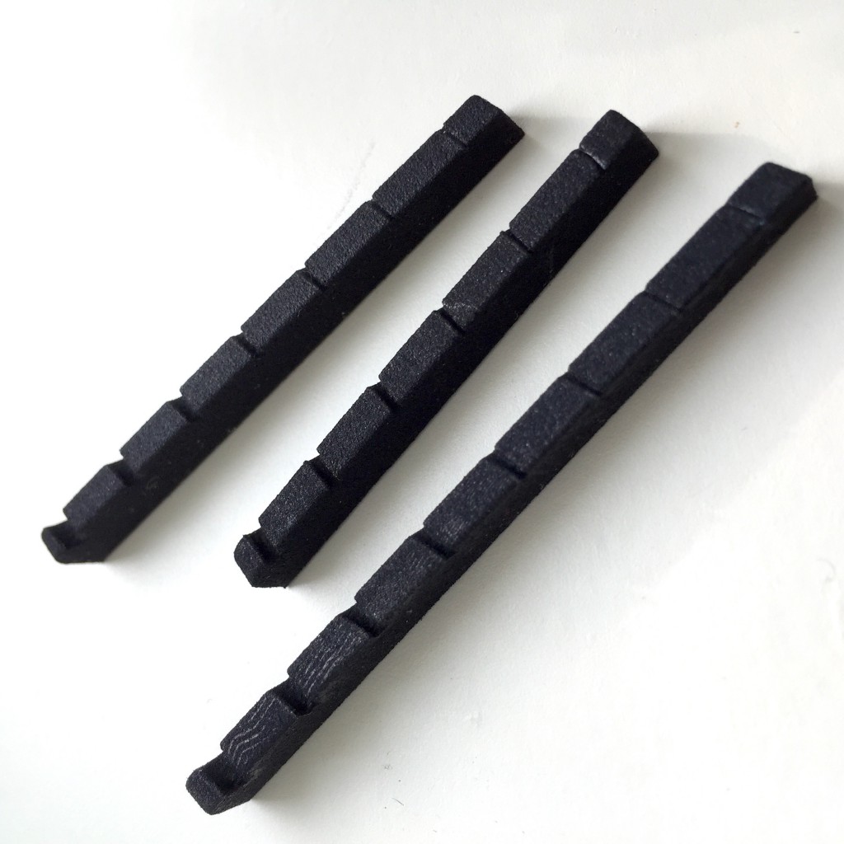
docs/3D Printed Nuts _ Strandberg Guitarworks_files/FullSizeRender-5-1024x1024.jpg
