FernandoB/strandberg/docs/db7 pickups/ALUMA-SPLIT_Wiring_0c92e320-4d51-46d5-88b3-a574761d29f3_1024x1024@2x.png

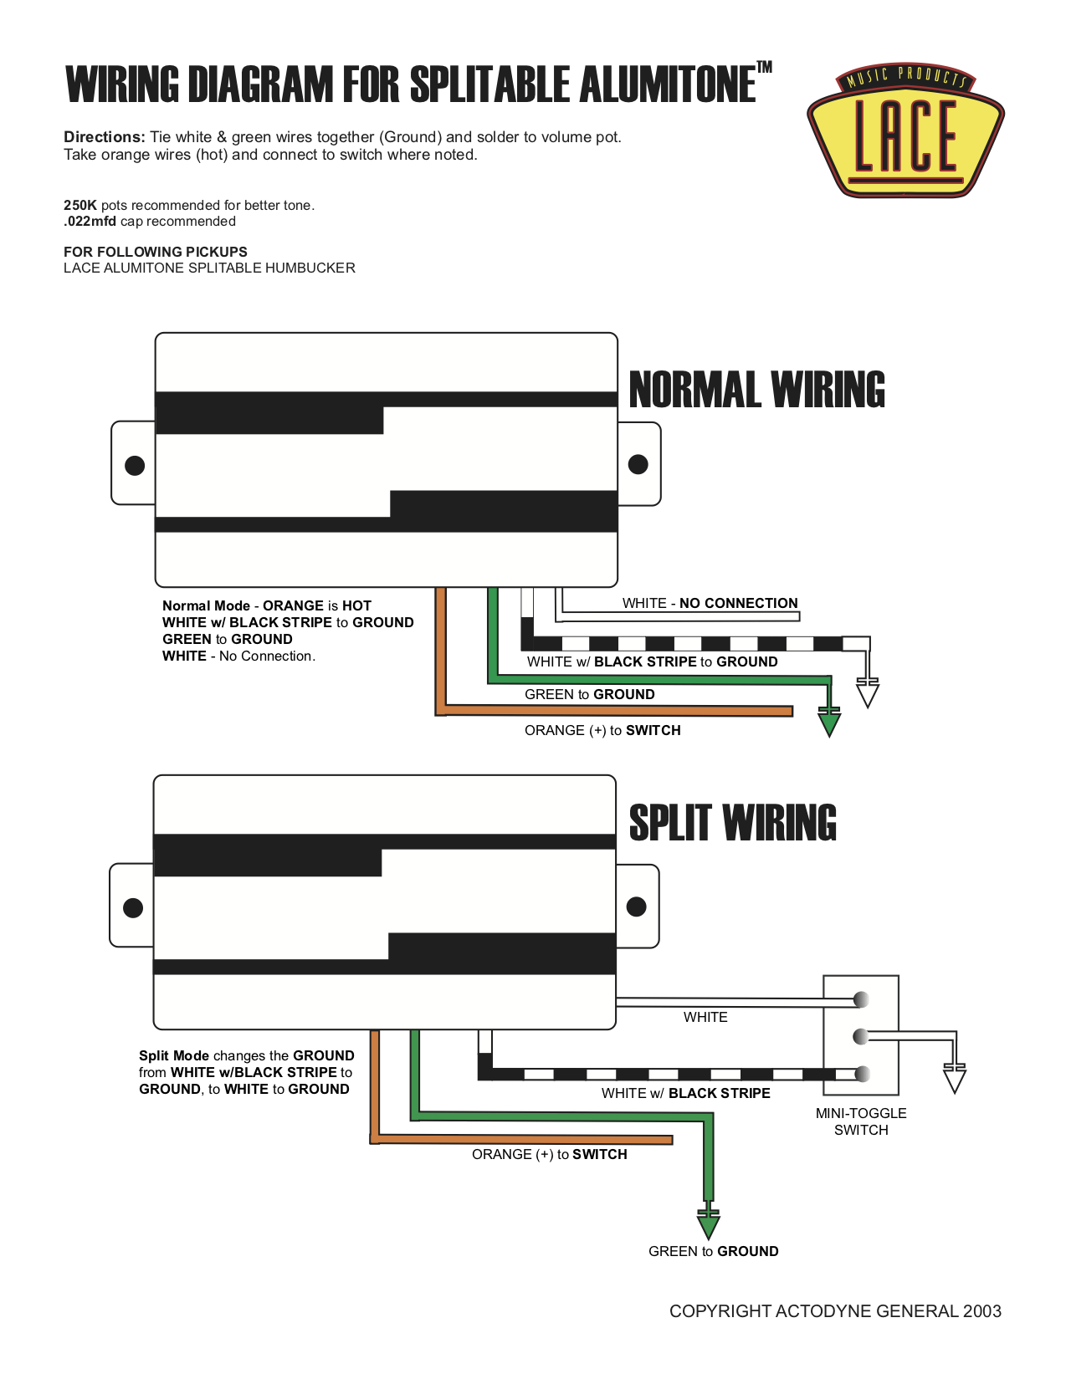
docs/db7 pickups/ALUMA-SPLIT_Wiring_0c92e320-4d51-46d5-88b3-a574761d29f3_1024x1024@2x.png
