FernandoB/strandberg/docs/Design and Build a Custom Electric Guitar_ 19 Steps (with Pictures)_files/F0F8TZRIWH3HFEV.MEDIUM.jpg

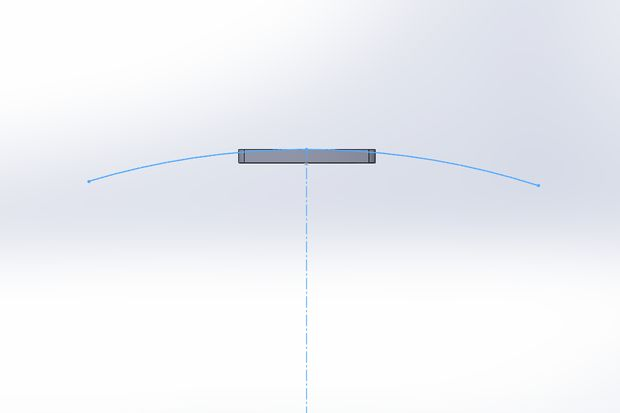
docs/Design and Build a Custom Electric Guitar_ 19 Steps (with Pictures)_files/F0F8TZRIWH3HFEV.MEDIUM.jpg
