FernandoB/strandberg/docs/Design and Build a Custom Electric Guitar_ 19 Steps (with Pictures)_files/F3G65HEIWH3HF65.MEDIUM.jpg

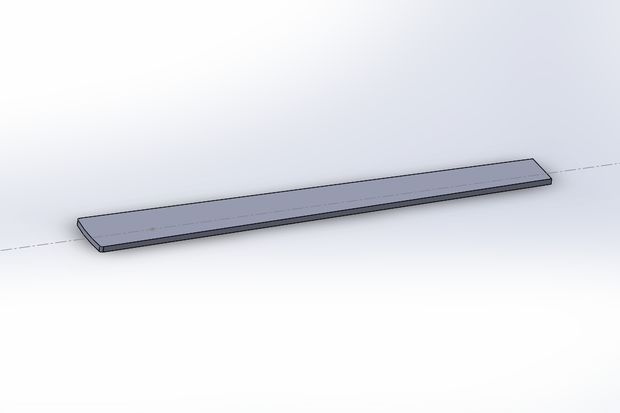
docs/Design and Build a Custom Electric Guitar_ 19 Steps (with Pictures)_files/F3G65HEIWH3HF65.MEDIUM.jpg
