FernandoB/strandberg/docs/Design and Build a Custom Electric Guitar_ 19 Steps (with Pictures)_files/F5KD9EOIWH3HG3H.MEDIUM.jpg

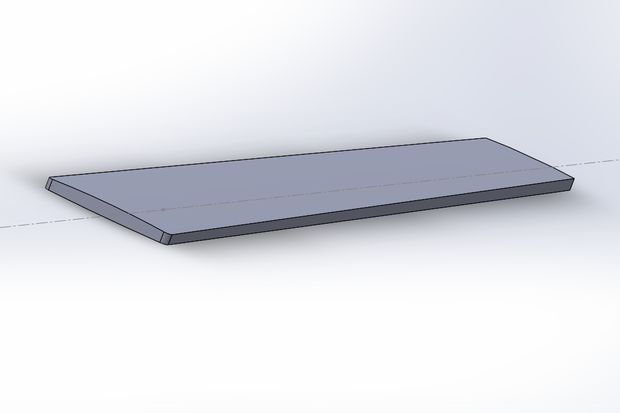
docs/Design and Build a Custom Electric Guitar_ 19 Steps (with Pictures)_files/F5KD9EOIWH3HG3H.MEDIUM.jpg
