FernandoB/strandberg/docs/Design and Build a Custom Electric Guitar_ 19 Steps (with Pictures)_files/F6QBIIYIWMQT1OU.SQUARE3.jpg

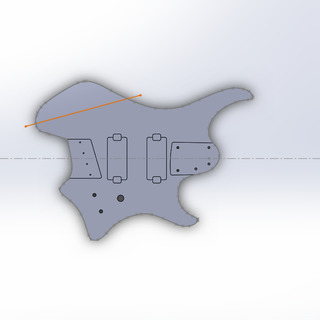
docs/Design and Build a Custom Electric Guitar_ 19 Steps (with Pictures)_files/F6QBIIYIWMQT1OU.SQUARE3.jpg
