FernandoB/strandberg/docs/Design and Build a Custom Electric Guitar_ 19 Steps (with Pictures)_files/F7FDSHTIWMQWK6P.MEDIUM.jpg

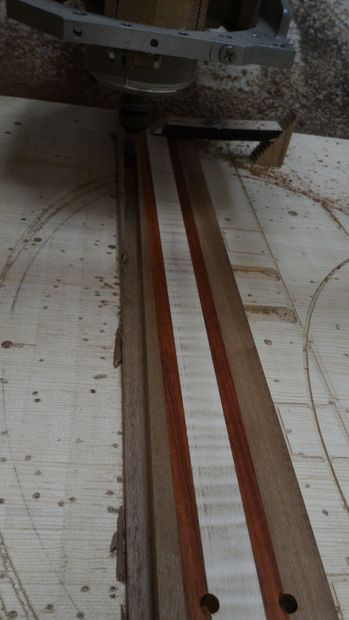
docs/Design and Build a Custom Electric Guitar_ 19 Steps (with Pictures)_files/F7FDSHTIWMQWK6P.MEDIUM.jpg
