FernandoB/strandberg/docs/Design and Build a Custom Electric Guitar_ 19 Steps (with Pictures)_files/FA289F6IWMQT19M.SQUARE3.jpg

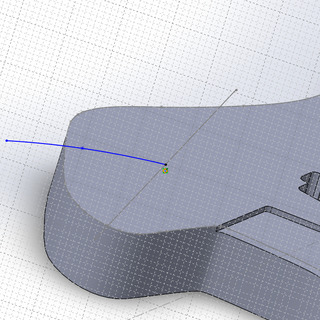
docs/Design and Build a Custom Electric Guitar_ 19 Steps (with Pictures)_files/FA289F6IWMQT19M.SQUARE3.jpg
