FernandoB/strandberg/docs/Design and Build a Custom Electric Guitar_ 19 Steps (with Pictures)_files/FA947D6IWMR118G.LARGE.jpg

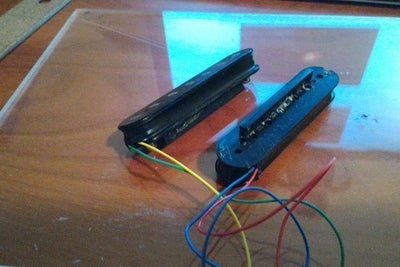
docs/Design and Build a Custom Electric Guitar_ 19 Steps (with Pictures)_files/FA947D6IWMR118G.LARGE.jpg
