FernandoB/strandberg/docs/Design and Build a Custom Electric Guitar_ 19 Steps (with Pictures)_files/FABEQEMIVO4GDQ9.png

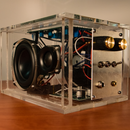
docs/Design and Build a Custom Electric Guitar_ 19 Steps (with Pictures)_files/FABEQEMIVO4GDQ9.png
