FernandoB/strandberg/docs/Design and Build a Custom Electric Guitar_ 19 Steps (with Pictures)_files/FEK32SBIWMR1Y50.LARGE.jpg

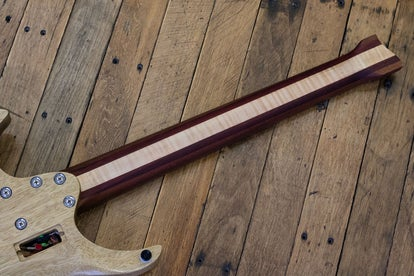
docs/Design and Build a Custom Electric Guitar_ 19 Steps (with Pictures)_files/FEK32SBIWMR1Y50.LARGE.jpg
