FernandoB/strandberg/docs/Design and Build a Custom Electric Guitar_ 19 Steps (with Pictures)_files/FF06RHUIWMR1183.LARGE.jpg

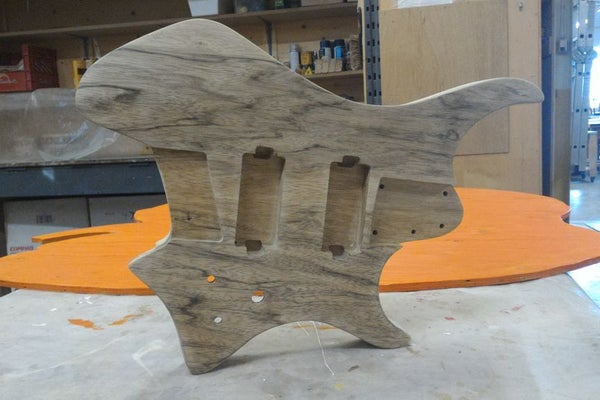
docs/Design and Build a Custom Electric Guitar_ 19 Steps (with Pictures)_files/FF06RHUIWMR1183.LARGE.jpg
