FernandoB/strandberg/docs/Design and Build a Custom Electric Guitar_ 19 Steps (with Pictures)_files/FFQRWO7IWMQWI9K.SQUARE3.jpg

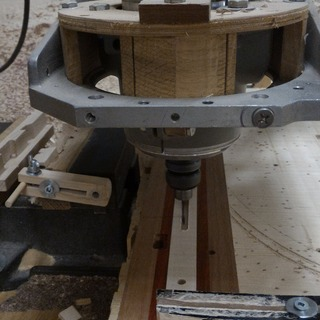
docs/Design and Build a Custom Electric Guitar_ 19 Steps (with Pictures)_files/FFQRWO7IWMQWI9K.SQUARE3.jpg
