FernandoB/strandberg/docs/Design and Build a Custom Electric Guitar_ 19 Steps (with Pictures)_files/FGEVUU2IWMQT1A6.SQUARE3.jpg

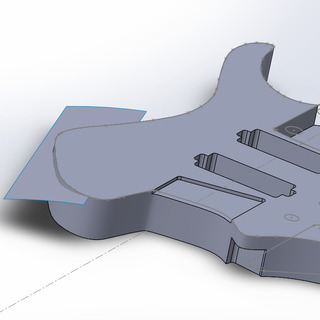
docs/Design and Build a Custom Electric Guitar_ 19 Steps (with Pictures)_files/FGEVUU2IWMQT1A6.SQUARE3.jpg
