FernandoB/strandberg/docs/Design and Build a Custom Electric Guitar_ 19 Steps (with Pictures)_files/FGGQ2NXIWMQT1AS.SQUARE3.jpg

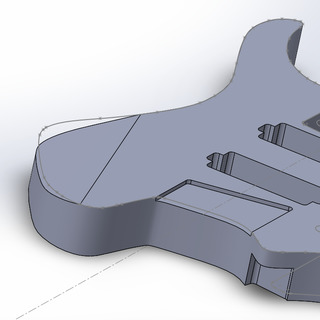
docs/Design and Build a Custom Electric Guitar_ 19 Steps (with Pictures)_files/FGGQ2NXIWMQT1AS.SQUARE3.jpg
