FernandoB/strandberg/docs/Design and Build a Custom Electric Guitar_ 19 Steps (with Pictures)_files/FHGDFY8IVO39YET.jpg

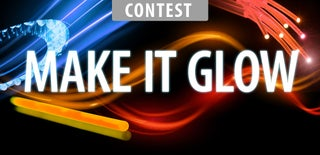
docs/Design and Build a Custom Electric Guitar_ 19 Steps (with Pictures)_files/FHGDFY8IVO39YET.jpg
