FernandoB/strandberg/docs/Design and Build a Custom Electric Guitar_ 19 Steps (with Pictures)_files/FI3NXT4IWMR1180.LARGE.jpg

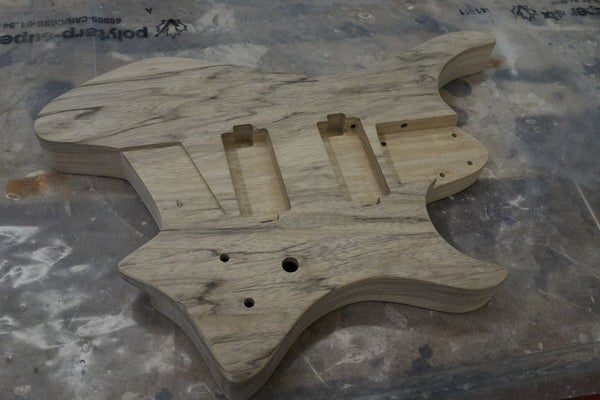
docs/Design and Build a Custom Electric Guitar_ 19 Steps (with Pictures)_files/FI3NXT4IWMR1180.LARGE.jpg
