FernandoB/strandberg/docs/Design and Build a Custom Electric Guitar_ 19 Steps (with Pictures)_files/FJP8P6AIWH3H4OF.SMALL.jpg

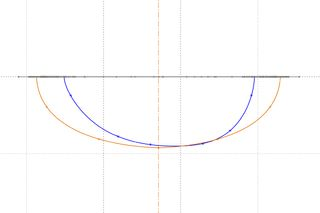
docs/Design and Build a Custom Electric Guitar_ 19 Steps (with Pictures)_files/FJP8P6AIWH3H4OF.SMALL.jpg
