FernandoB/strandberg/docs/Design and Build a Custom Electric Guitar_ 19 Steps (with Pictures)_files/FJTMRNUIWMR118H.LARGE.jpg

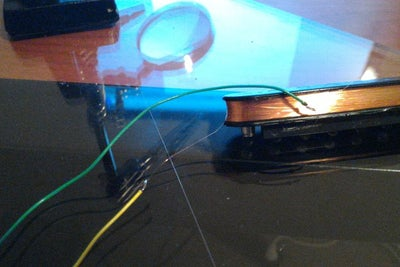
docs/Design and Build a Custom Electric Guitar_ 19 Steps (with Pictures)_files/FJTMRNUIWMR118H.LARGE.jpg
