FernandoB/strandberg/docs/Design and Build a Custom Electric Guitar_ 19 Steps (with Pictures)_files/FSOFWZCIVA4UDFN.jpg

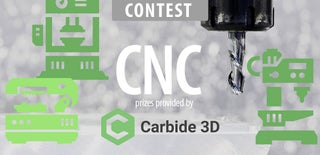
docs/Design and Build a Custom Electric Guitar_ 19 Steps (with Pictures)_files/FSOFWZCIVA4UDFN.jpg
