FernandoB/strandberg/docs/Design and Build a Custom Electric Guitar_ 19 Steps (with Pictures)_files/FXWS8RRIVO527G4.jpg

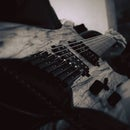
docs/Design and Build a Custom Electric Guitar_ 19 Steps (with Pictures)_files/FXWS8RRIVO527G4.jpg
