FernandoB/strandberg/docs/specs/Boden Classic 7 Ghost White _ .strandberg_ Guitars_files/guitar-measurements-strandberg-1.webp

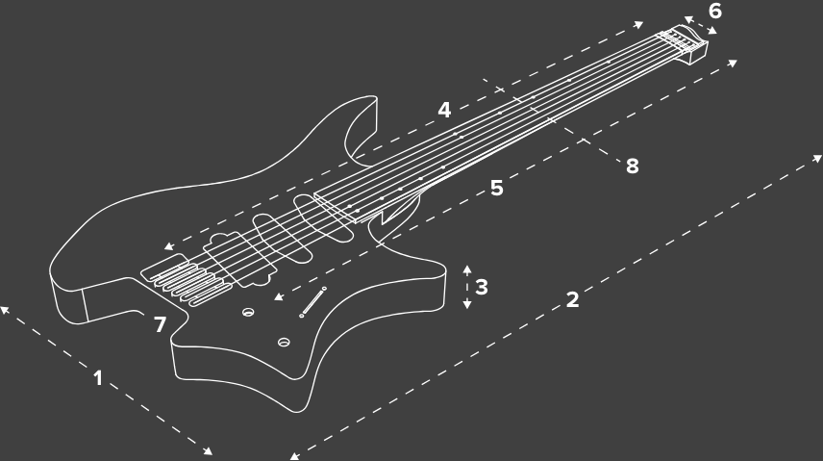
docs/specs/Boden Classic 7 Ghost White _ .strandberg_ Guitars_files/guitar-measurements-strandberg-1.webp
