FernandoB/strandberg/plano/plano_rockar/Strandberg Boden 8 Rockar Full.pdf

# 24 Frets SPECI

F

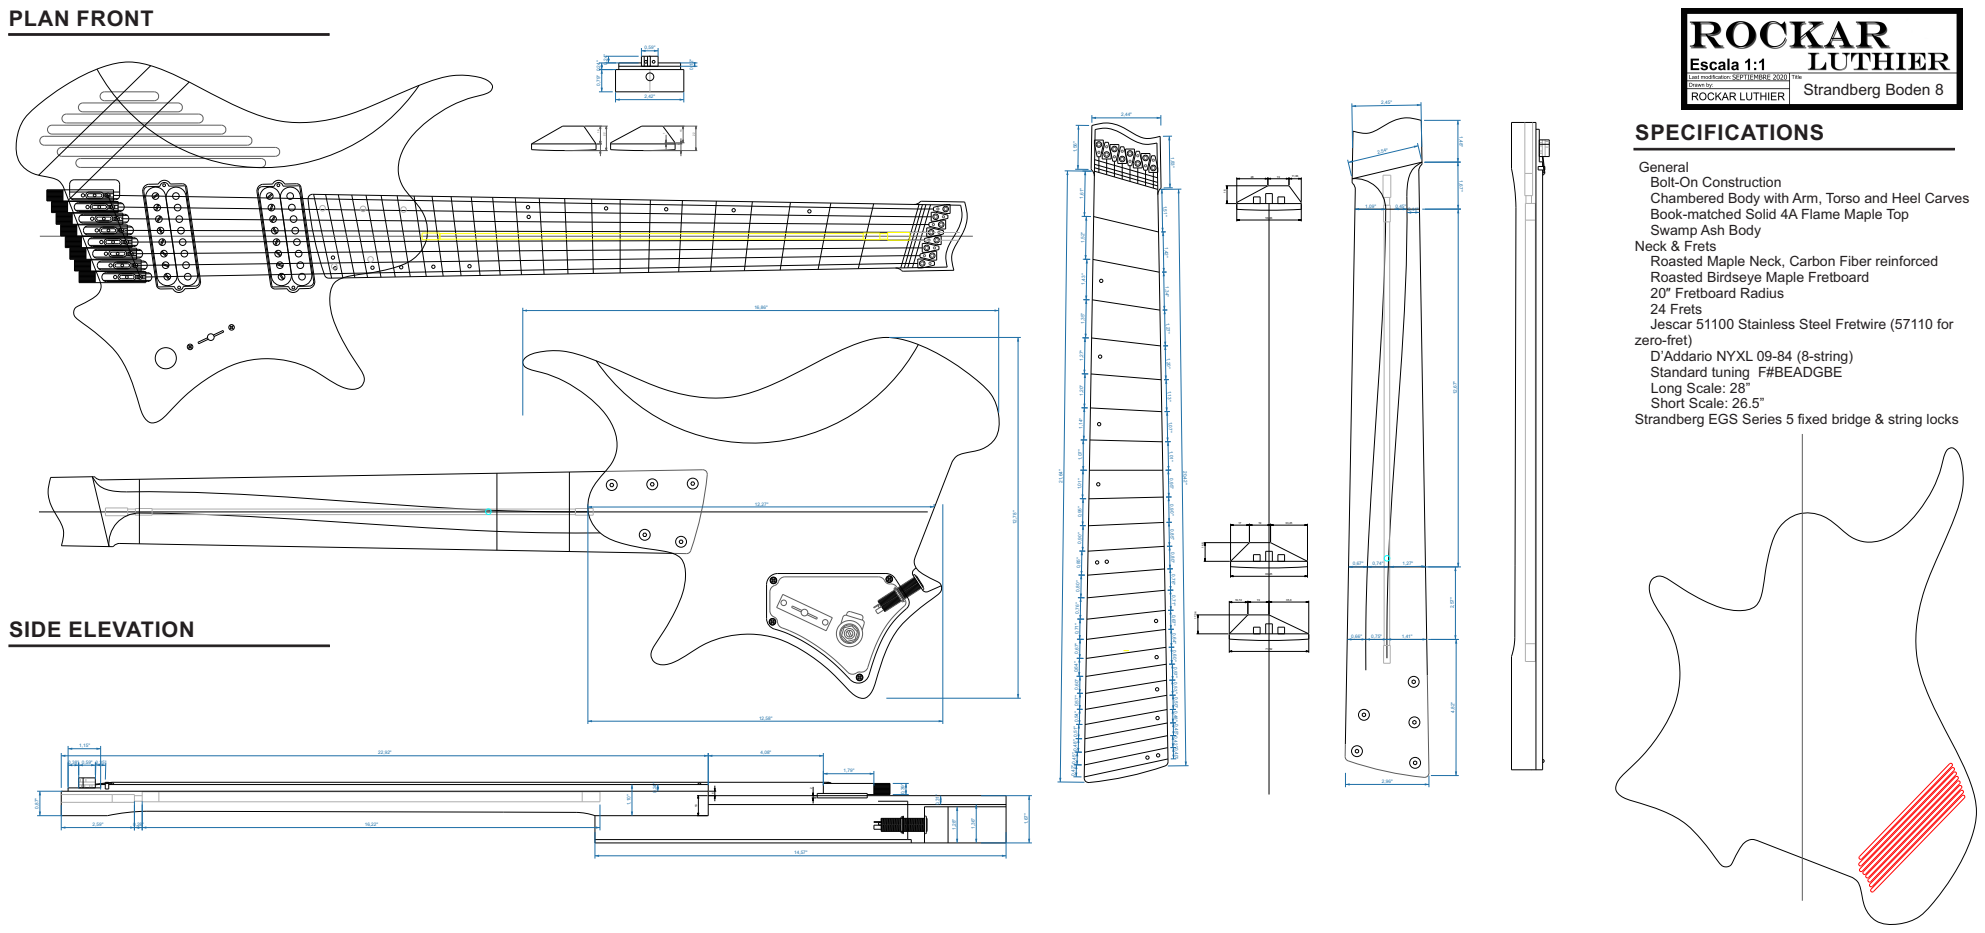
[picture p207: page 1]
Scale: 26.5”; Top; VAT; Strandberg Boden 8

General
Bolt-On Construction
Chambered Body with Arm,
Book-matched Solid 4A Flame Maple
Swamp Ash Body
Neck & Frets
Roasted Maple Neck, Carbon Fiber reinforced
Roasted Birdseye Maple Fretboard
20″ Fretboard Radius

Torso and Heel Carves

Jescar 51100 Stainless Steel Fretwire (57110 for
zero-fret)
D’Addario NYXL 09-84 (8-string)
Standard tuning F#BEADGBE
Scale: 28”
Long
Short
Strandberg EGS Series 5 fixed bridge & string locks
