FernandoB/strandberg/docs/pdf/egs-bridge.pdf

B

A

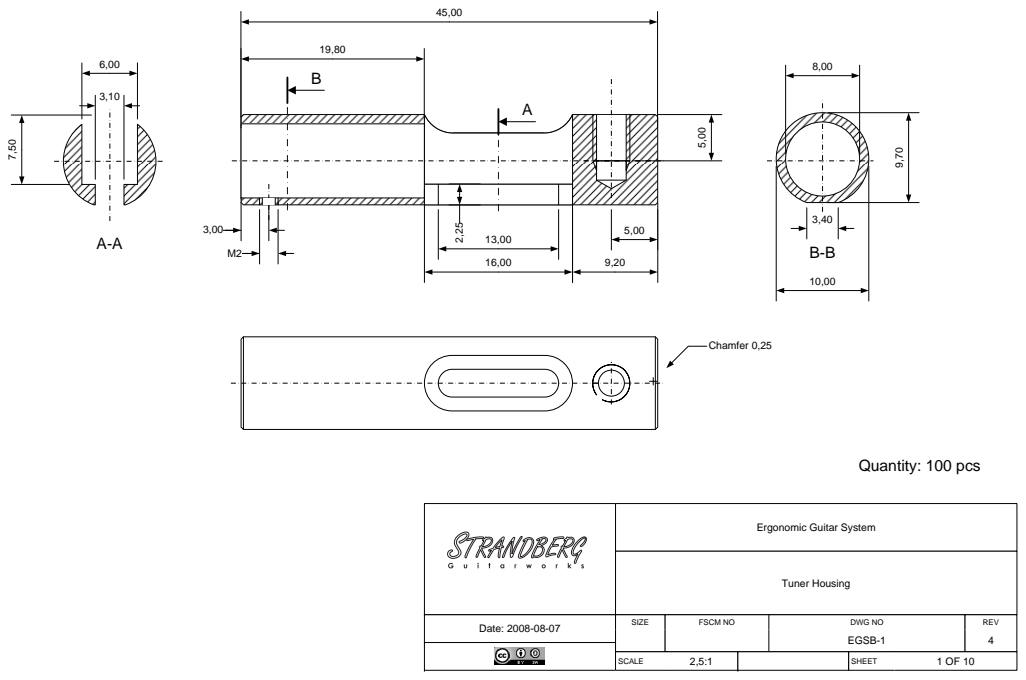
[picture p208: page 1]
Chamfer 0,25; Date: 2008-08-07; Tuner Housing; SIZE; FSCM NO; DWG NO; REV; EGSB-1; SCALE; SHEET; Quantity: 100 pcs

Ergonomic Guitar System

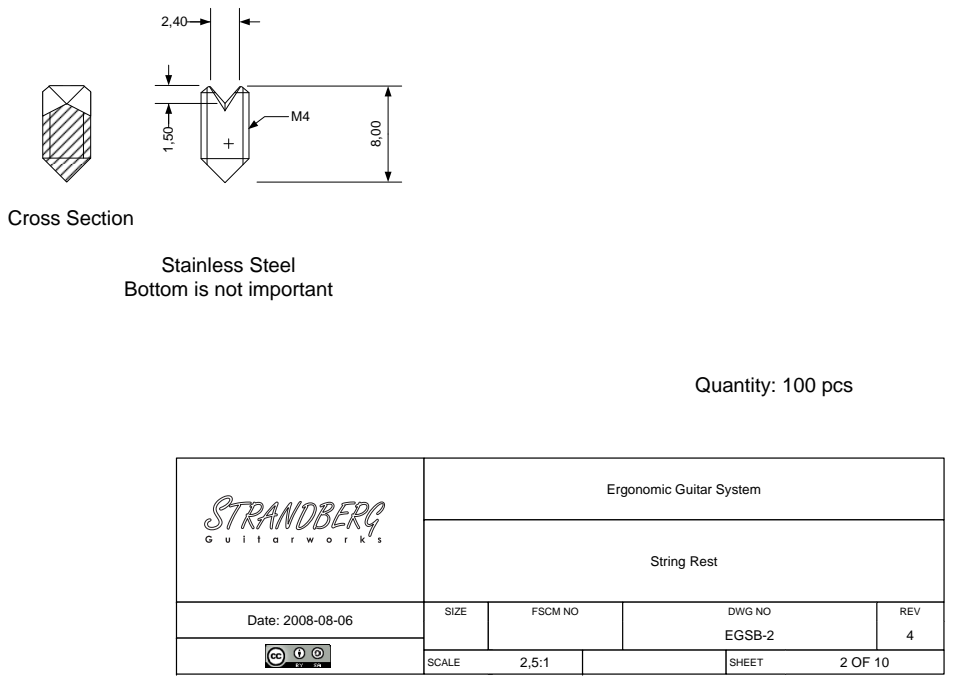
[picture p209: page 2]
Date: 2008-08-06; String Rest; SIZE; FSCM NO; DWG NO; REV; EGSB-2; SCALE; SHEET; Cross Section; Quantity: 100 pcs

Stainless Steel
Bottom is not important

Ergonomic Guitar System

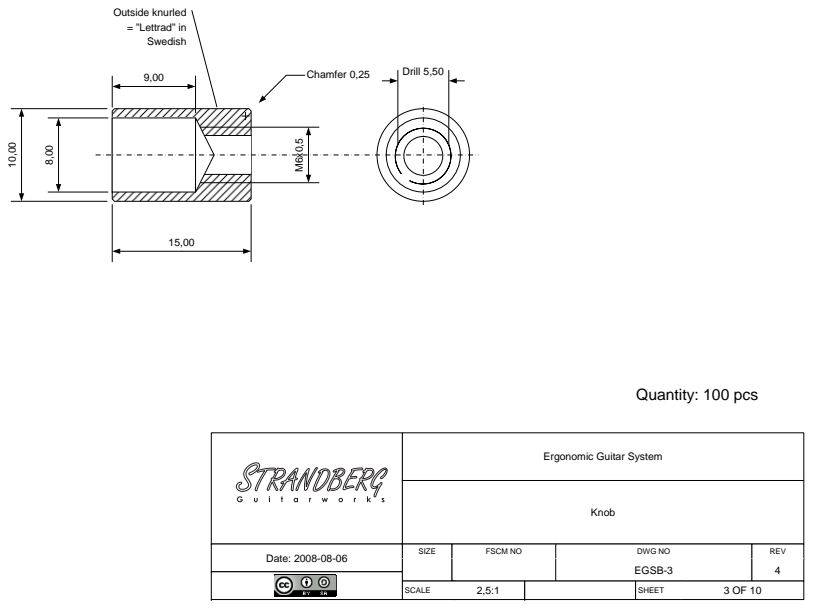
[picture p210: page 3]
Drill 5,50; Outside knurled = ”Lettrad” in Swedish; Chamfer 0,25; Date: 2008-08-06; Knob; SIZE; FSCM NO; DWG NO; REV; EGSB-3; SCALE; SHEET; Quantity: 100 pcs

Ergonomic Guitar System

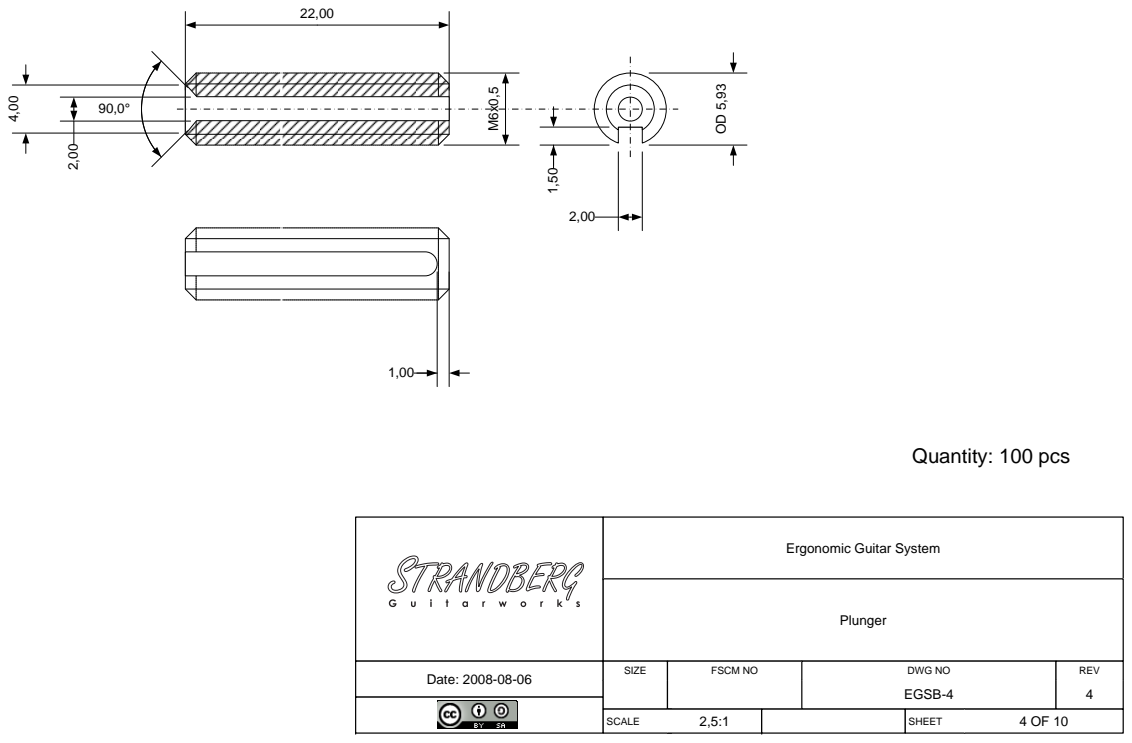
[picture p211: page 4]
Plunger; SIZE; FSCM NO; DWG NO; REV; EGSB-4; SCALE; SHEET; Quantity: 100 pcs

Ergonomic Guitar System

## Quantity: 15 pcs

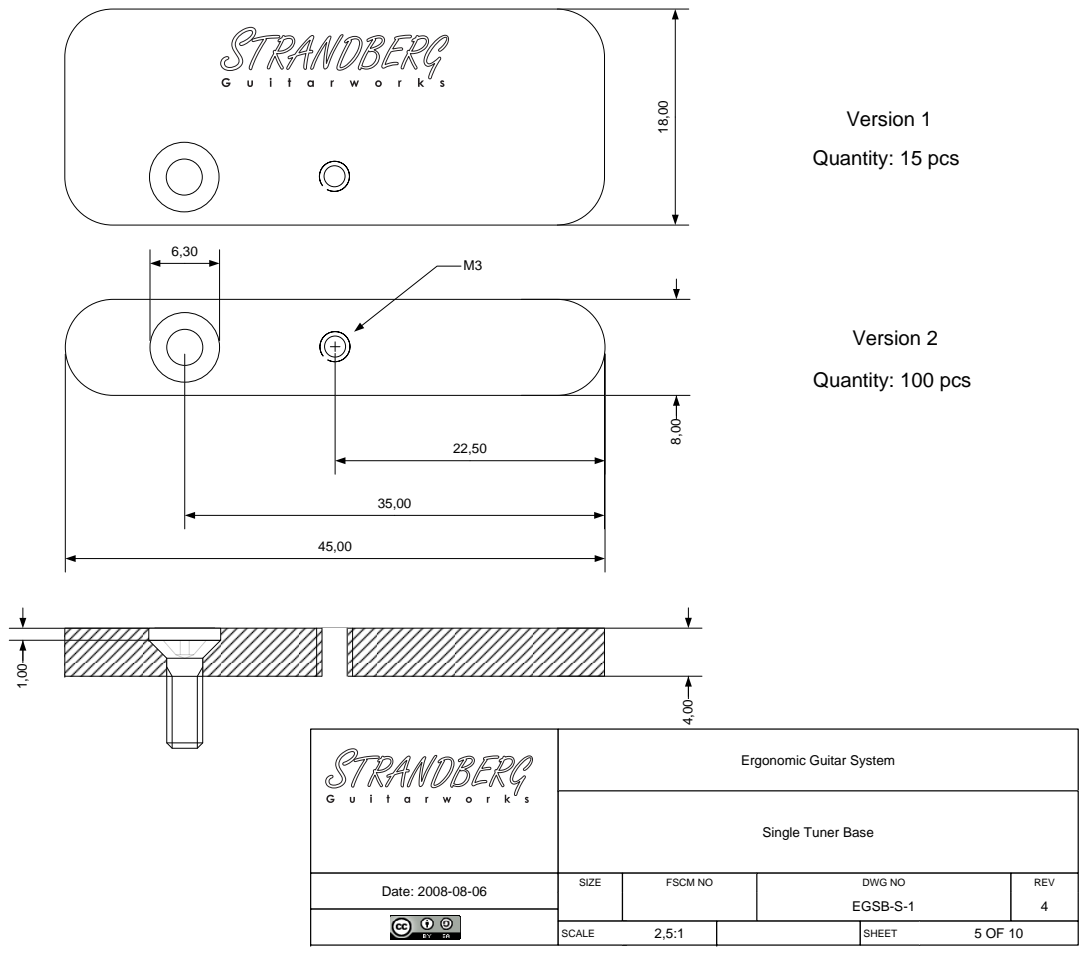
[picture p212: page 5]
SIZE; FSCM NO; DWG NO; REV; EGSB-S-1; SCALE; SHEET; 18,00 Version 1; Version 2; Quantity: 100 pcs

Ergonomic Guitar System

Single Tuner Base

A
B

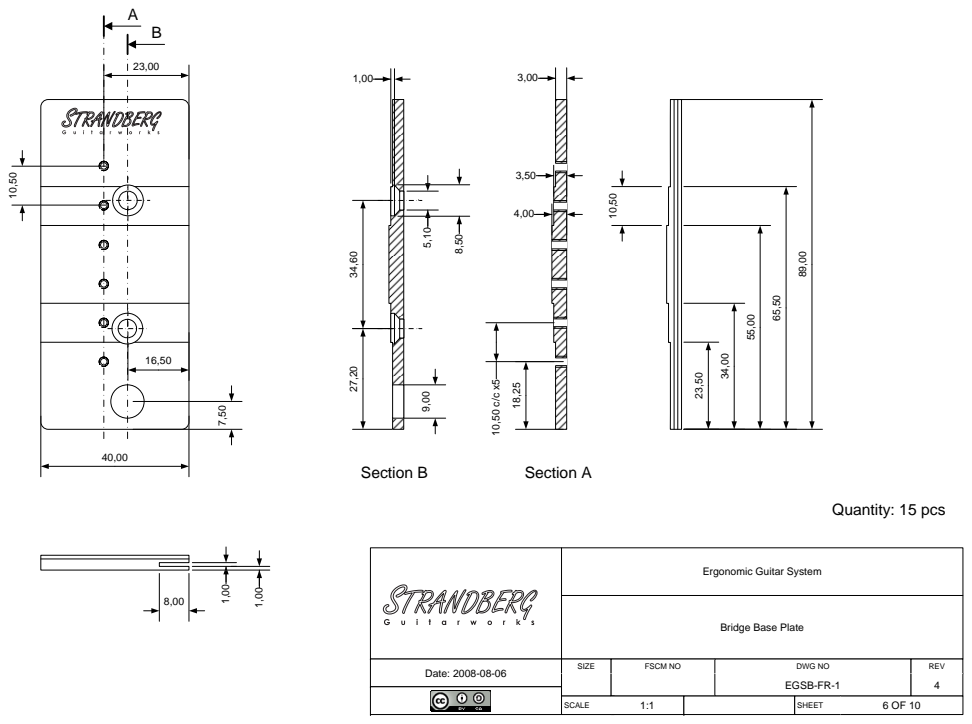
[picture p213: page 6]
SIZE; FSCM NO; DWG NO; REV; EGSB-FR-1; SCALE; SHEET; Section B; Section A; Quantity: 15 pcs

Ergonomic Guitar System

Bridge Base Plate

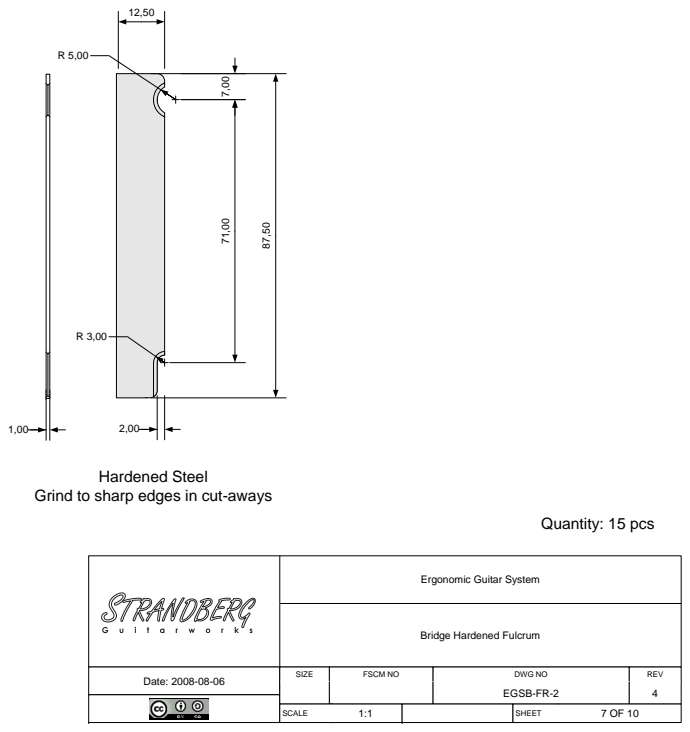
[picture p214: page 7]
SIZE; FSCM NO; DWG NO; REV; EGSB-FR-2; SCALE; SHEET; Hardened Steel; Quantity: 15 pcs

Grind to sharp edges in cut-aways

Ergonomic Guitar System

Bridge Hardened Fulcrum

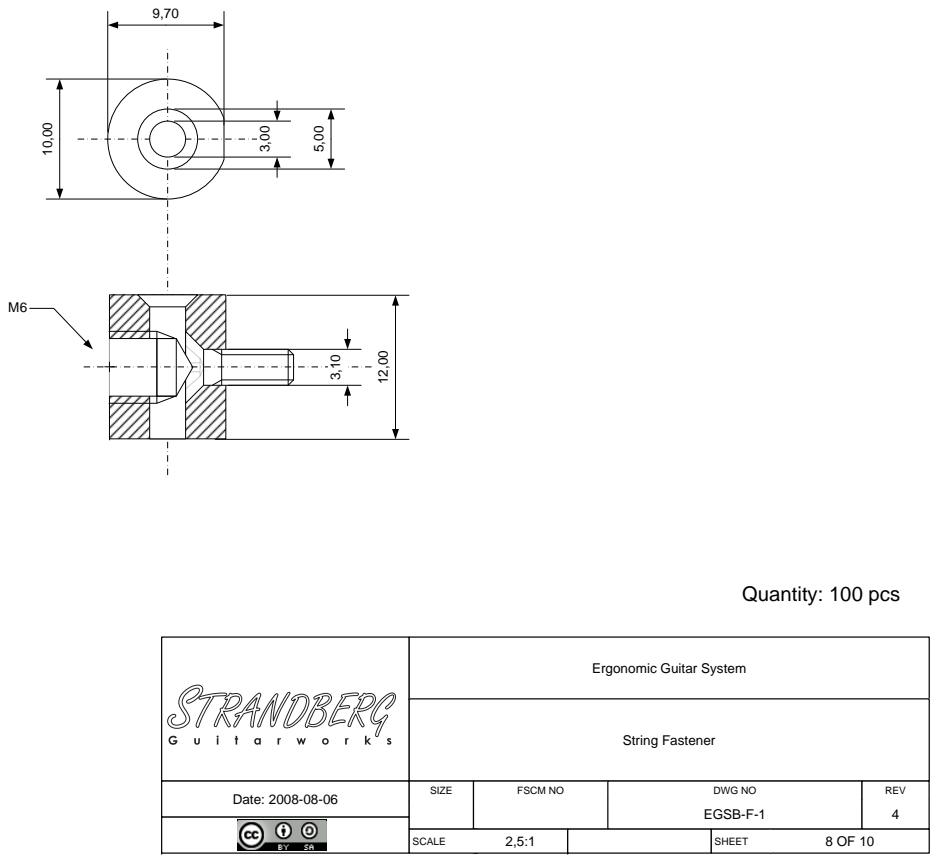
[picture p215: page 8]
Date: 2008-08-06; String Fastener; SIZE; FSCM NO; DWG NO; REV; EGSB-F-1; SCALE; SHEET; Quantity: 100 pcs

Ergonomic Guitar System
