FernandoB/strandberg/plano/plano_rockar/Template Strandberg Boden 8 Rockar.pdf

# Strandberg Boden 8

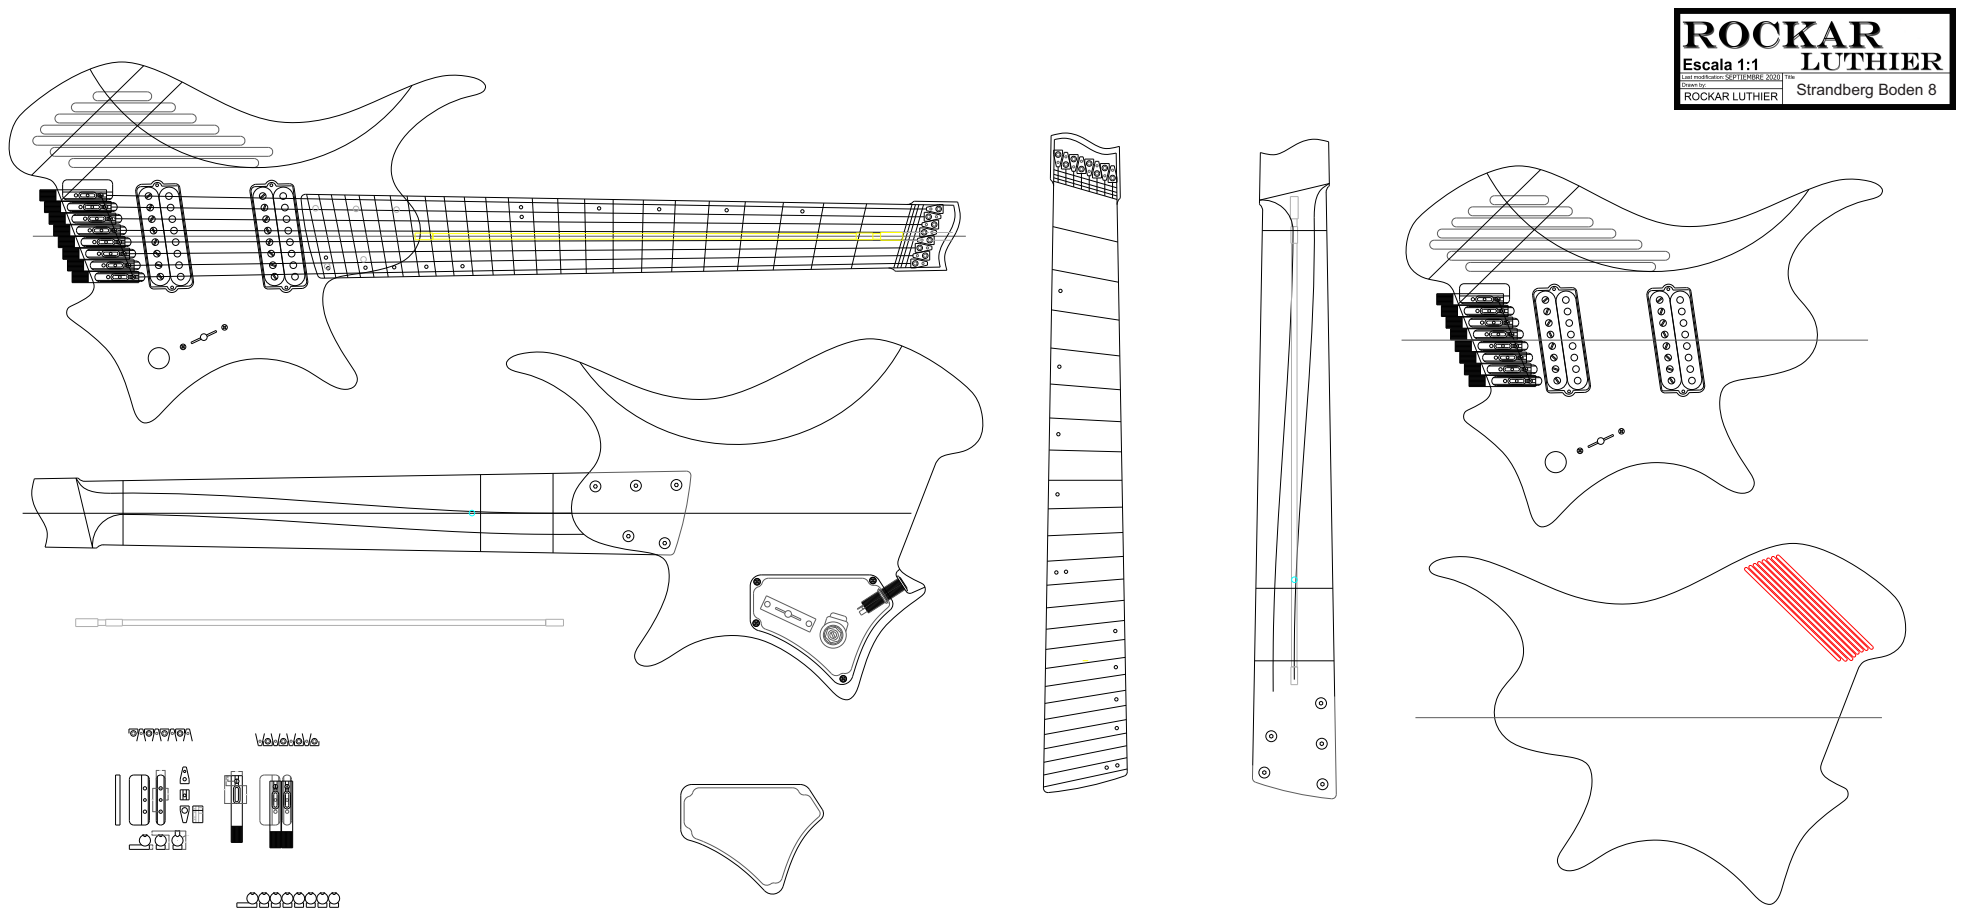
[picture p218: page 1]
