FernandoB/strandberg/photos/20230725_215624.jpg

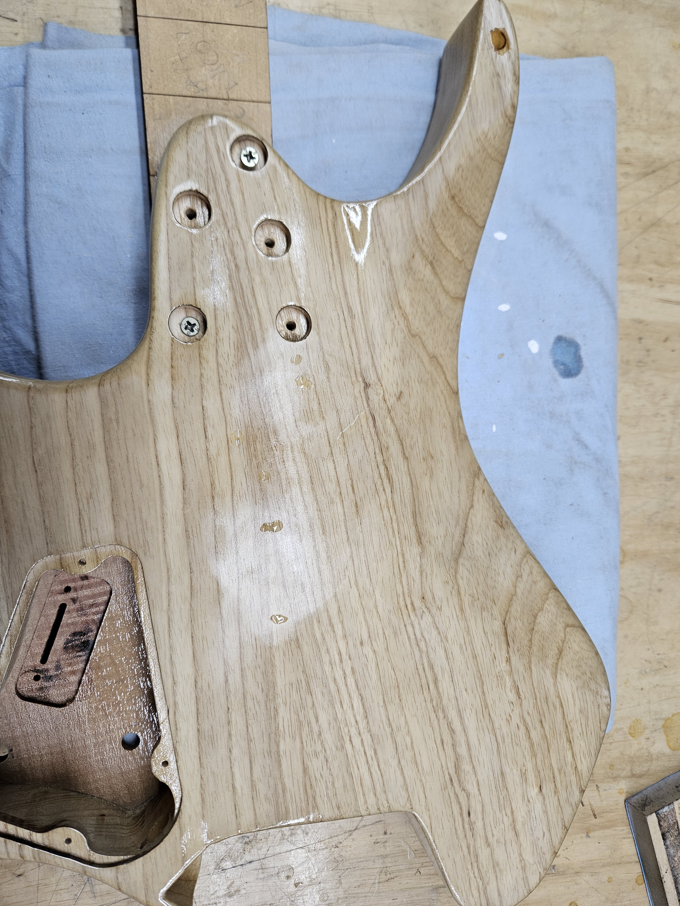
photos/20230725_215624.jpg
