FernandoB/strandberg/photos/20230829_215427.jpg

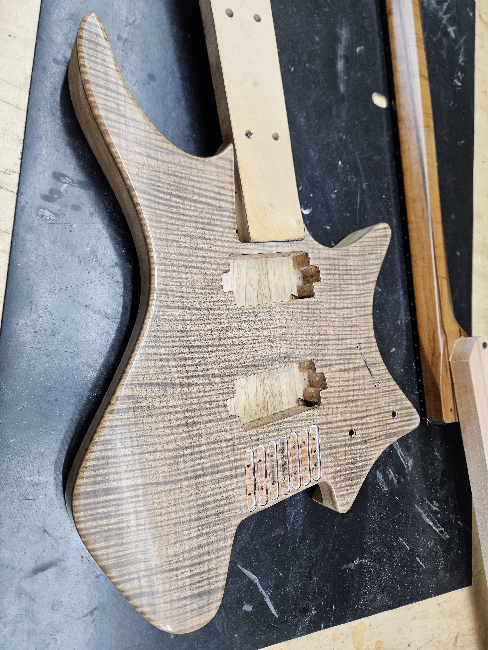
photos/20230829_215427.jpg
